patrickiel/pull-up-bar/cad/pull-up bar variants/biacromia breadth 37 cm (14.6 inch).pdf

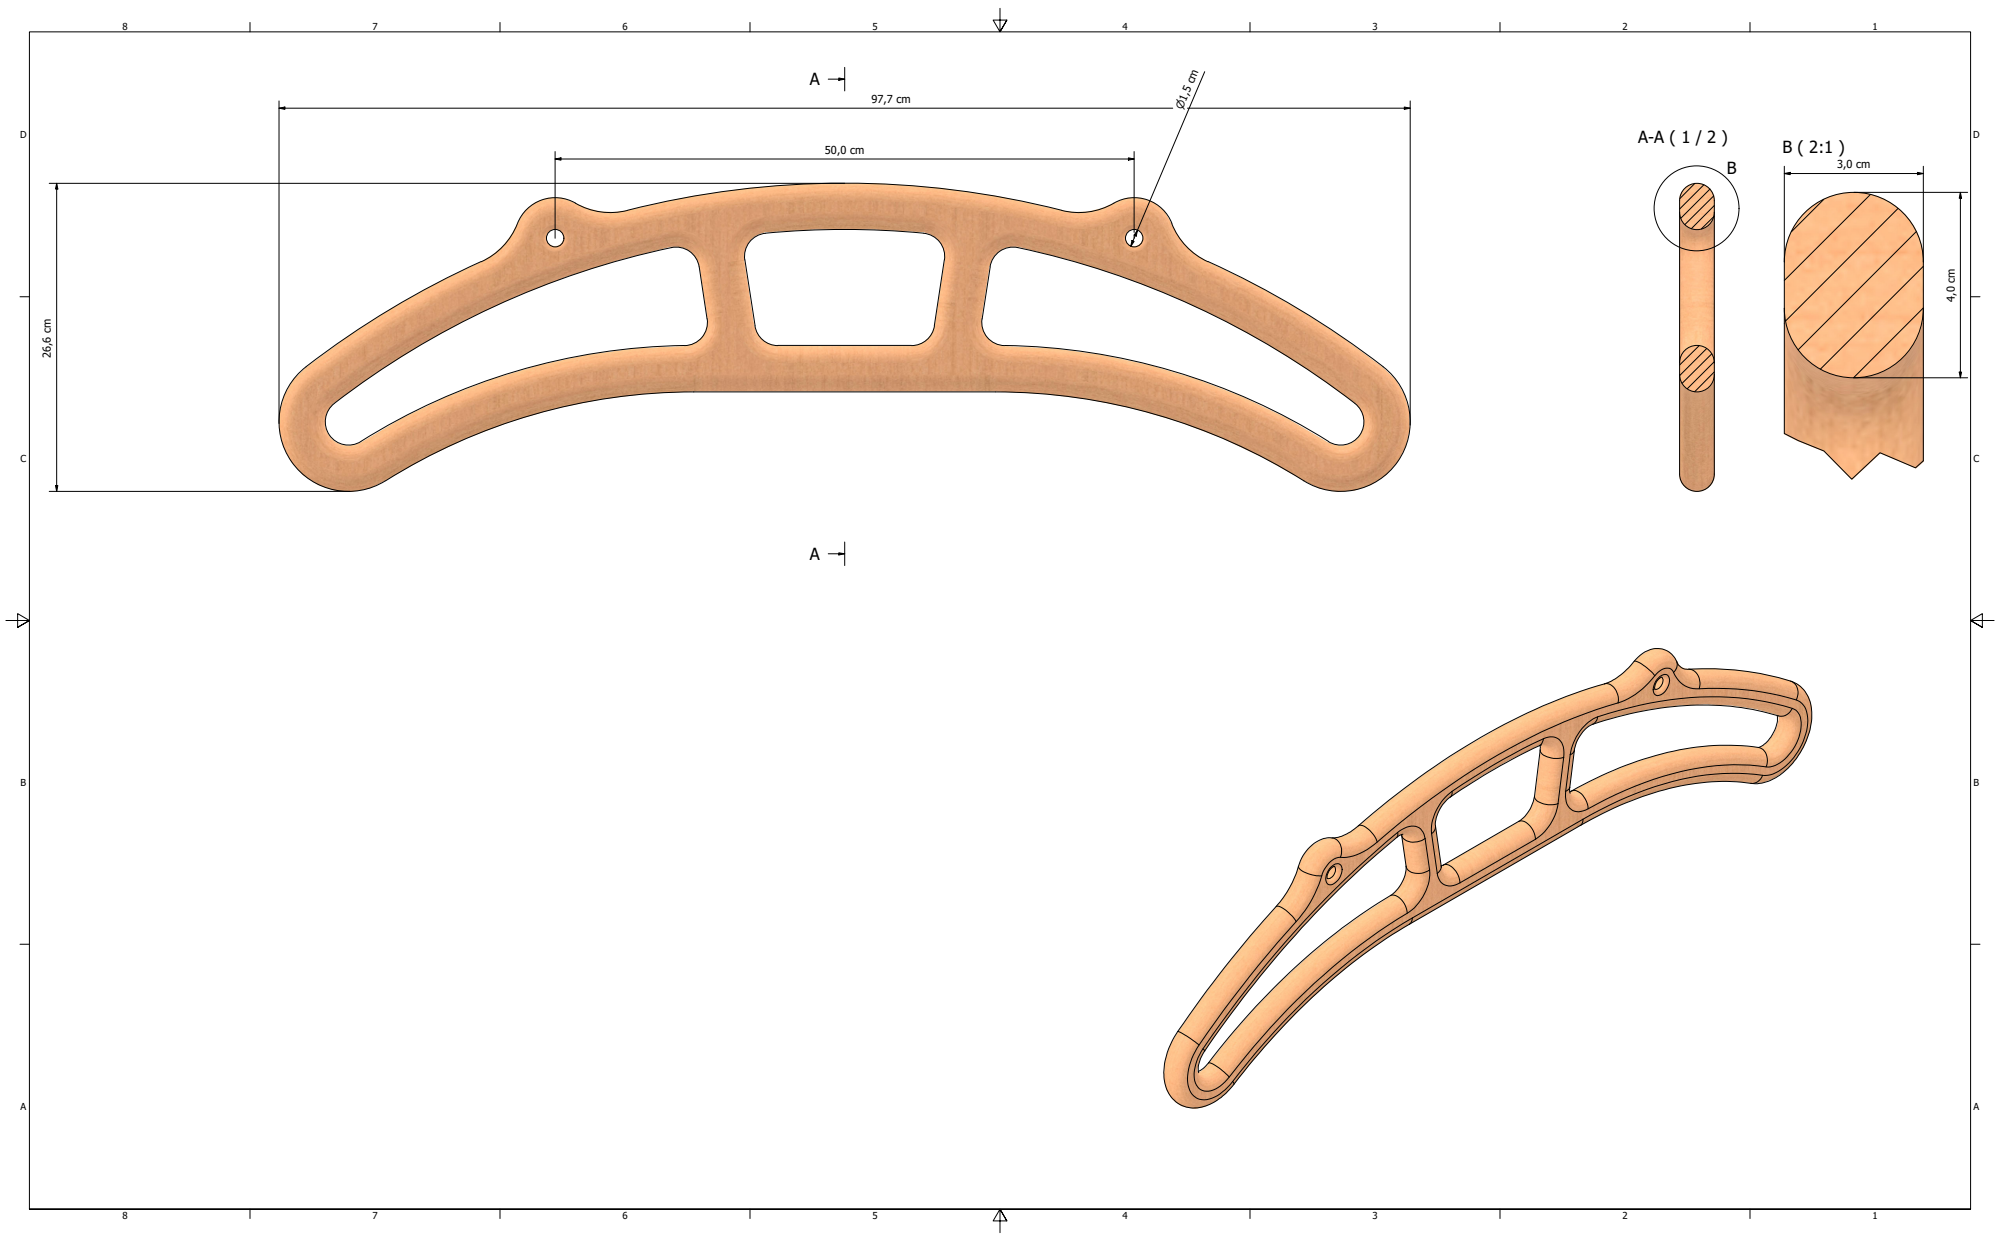
[picture p32: page 1]

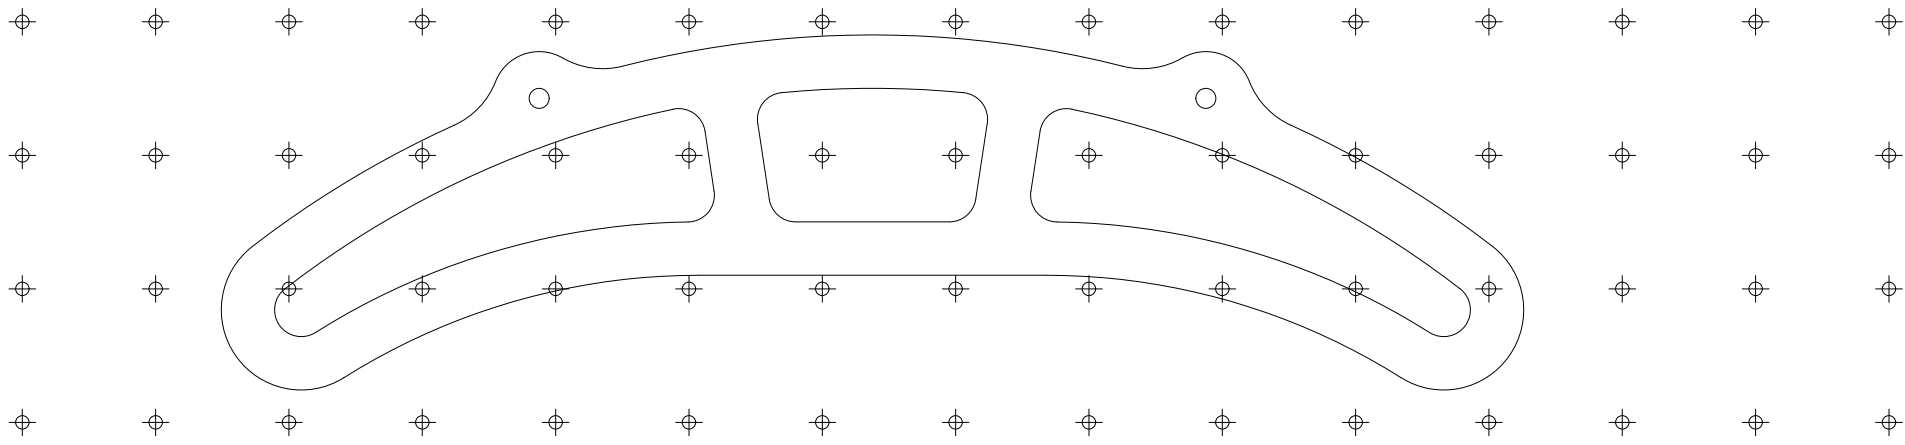
[picture p33: page 2]
