patrickiel/pull-up-bar/cad/pull-up bar variants/biacromia breadth 38 cm (15 inch).pdf

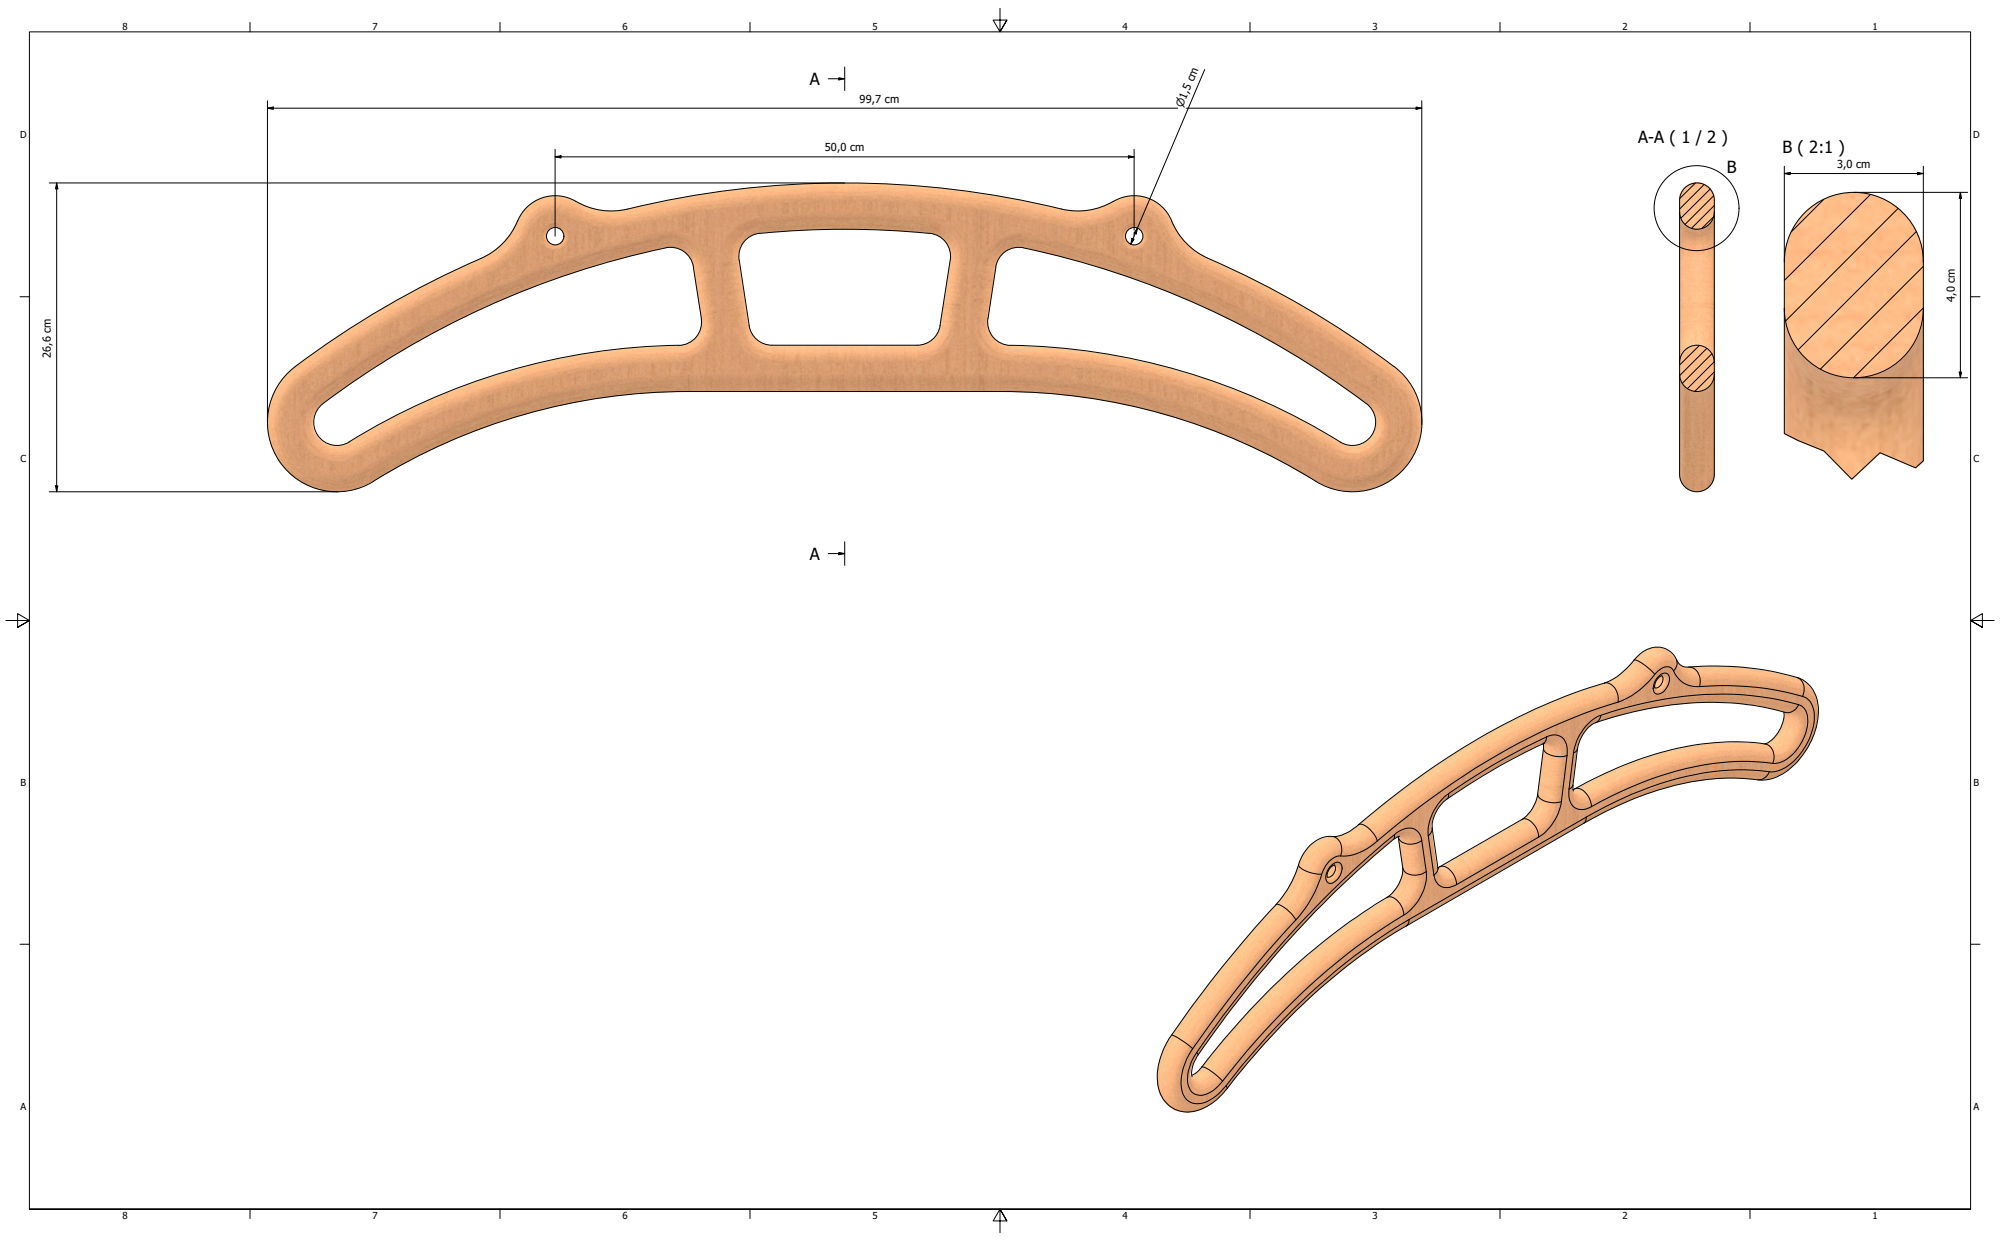
[picture p34: page 1]

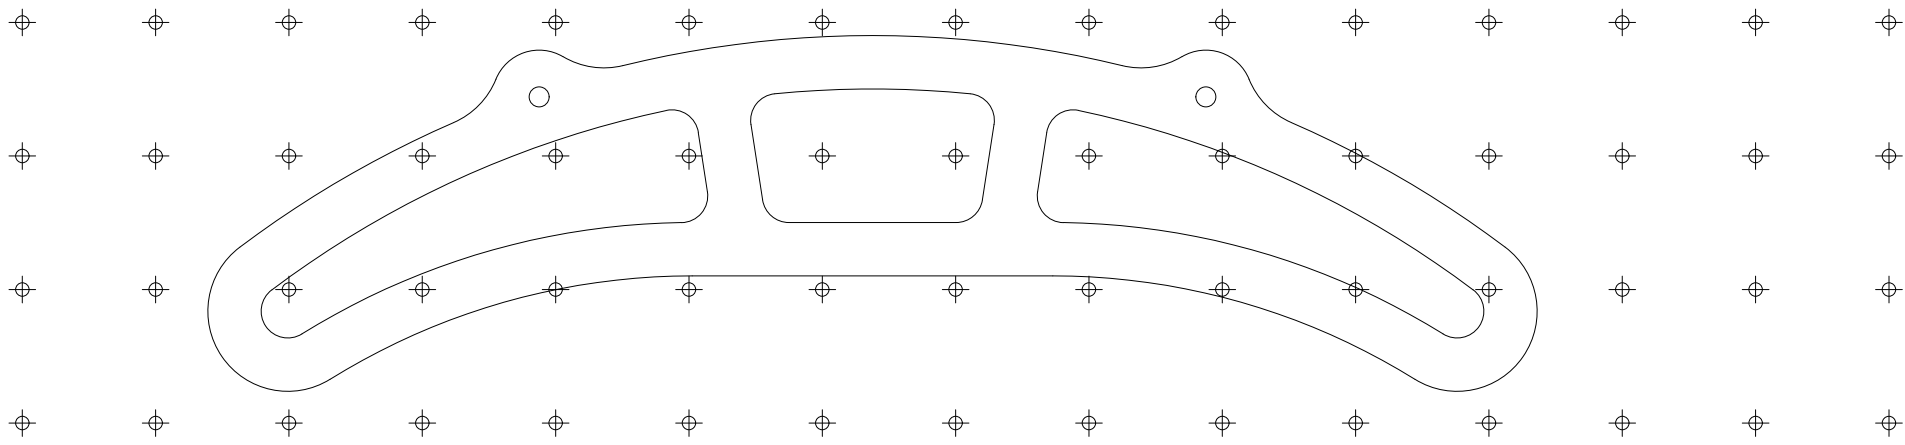
[picture p35: page 2]
