patrickiel/pull-up-bar/cad/pull-up bar variants/biacromia breadth 39 cm (15.4 inch).pdf

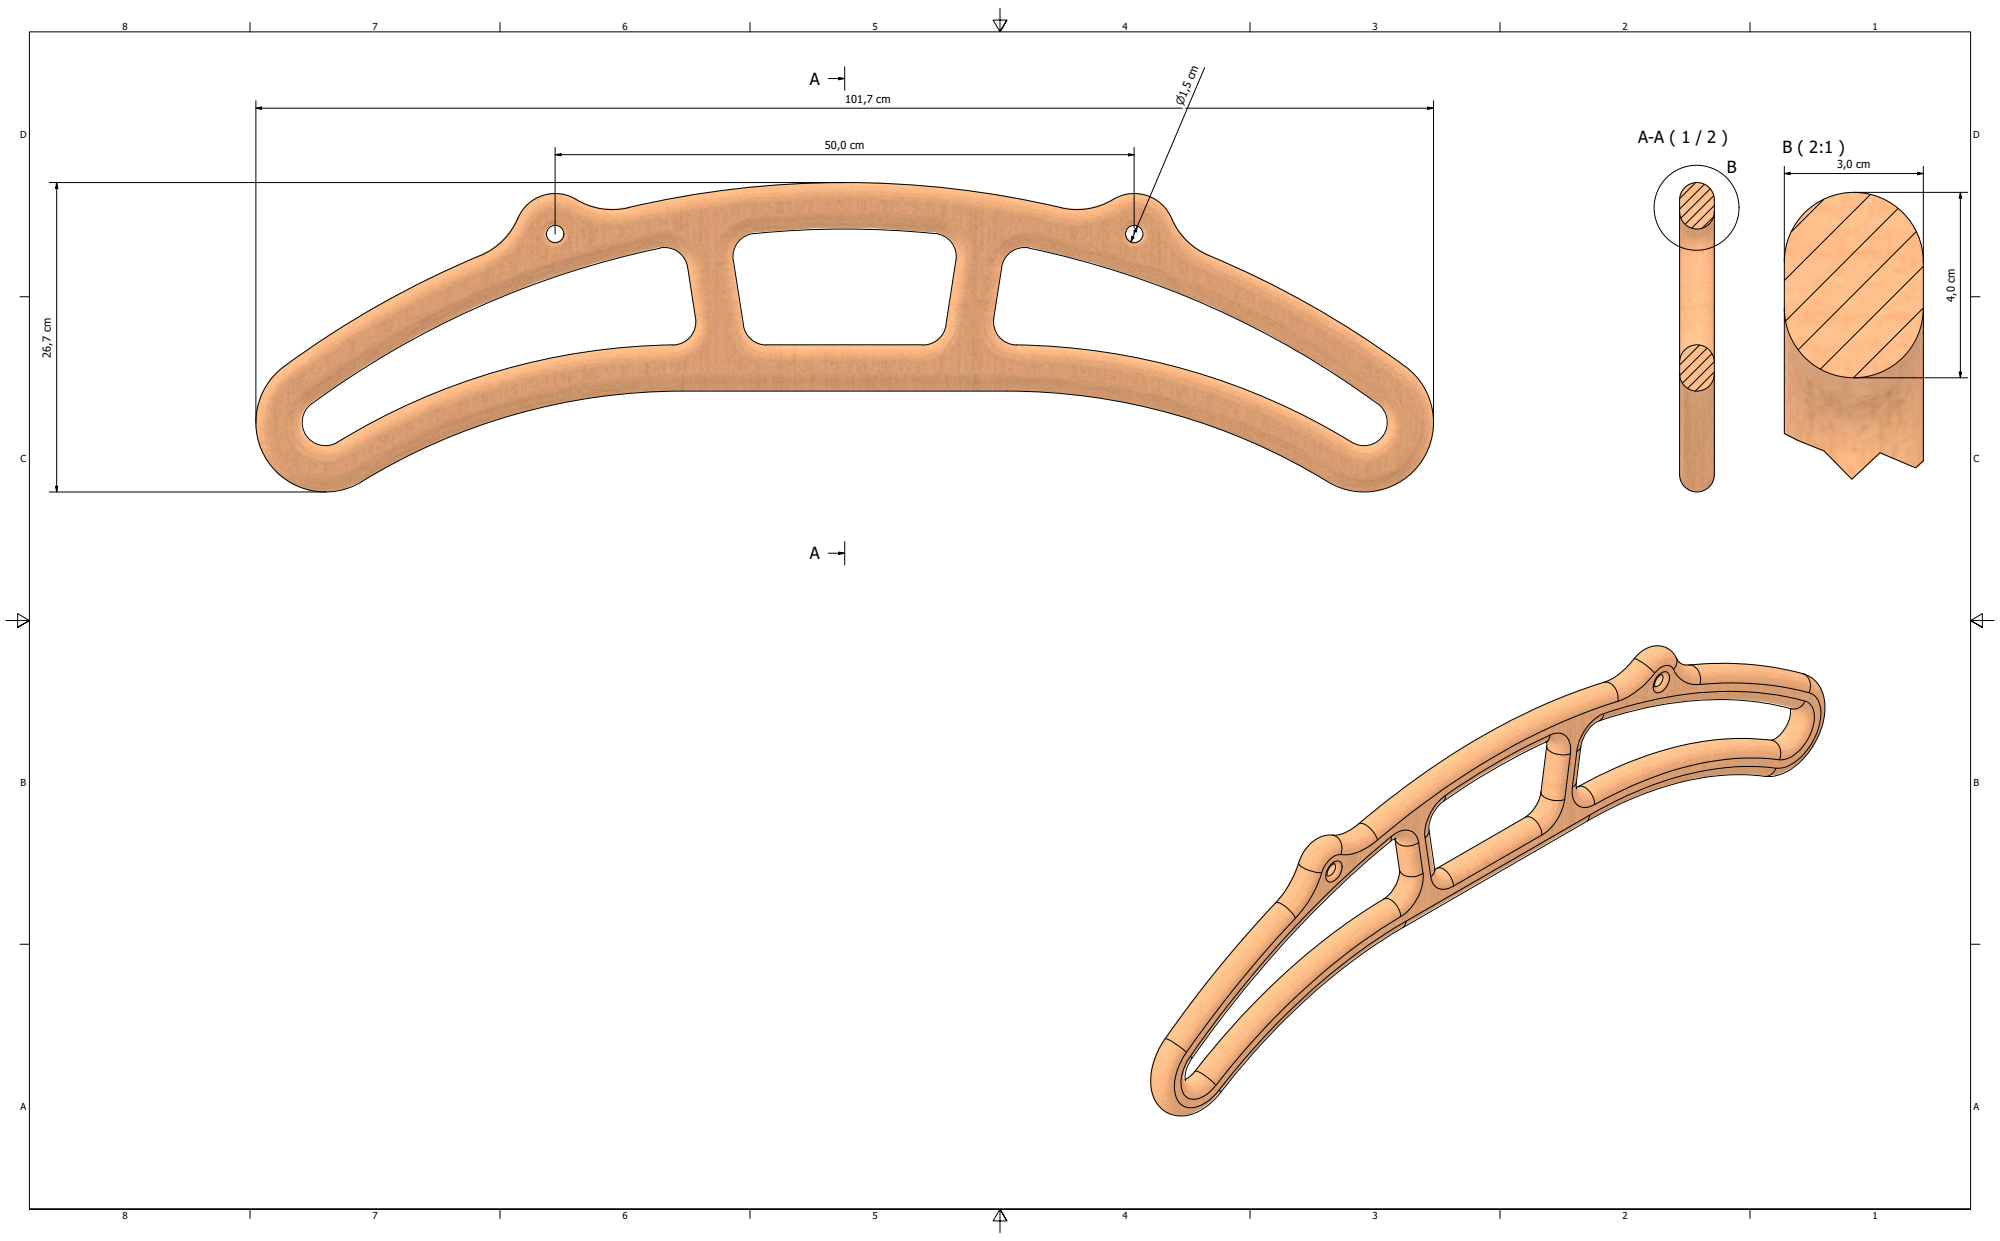
[picture p36: page 1]

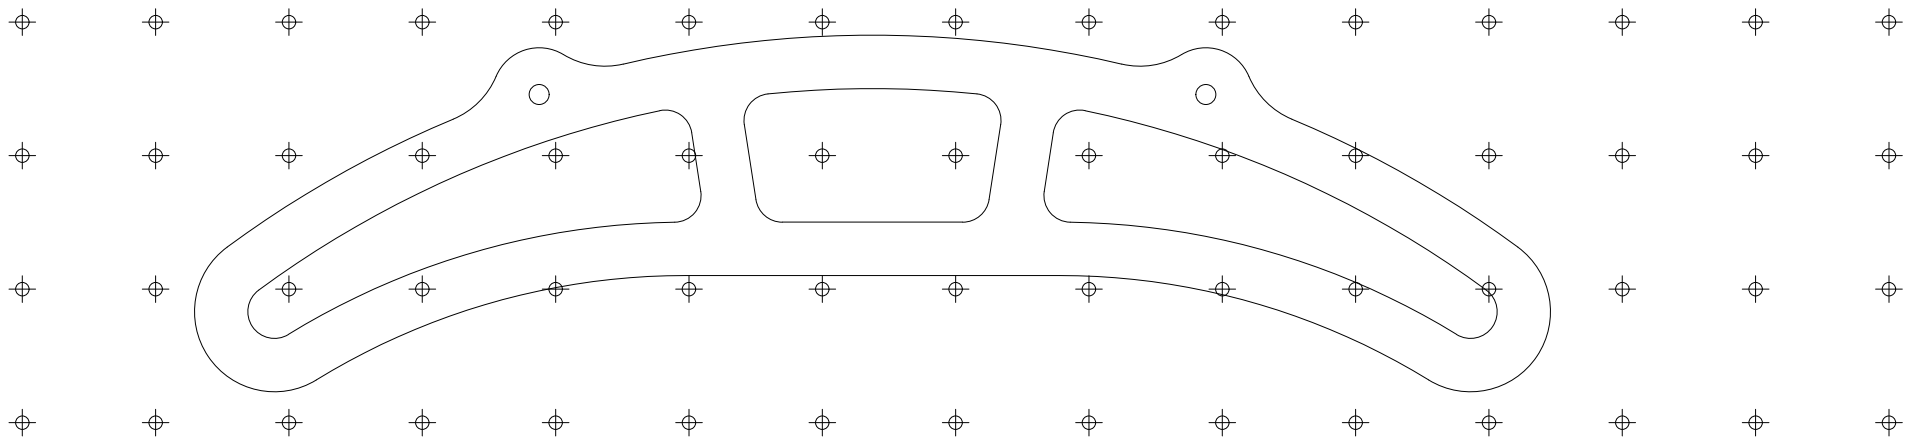
[picture p37: page 2]
