patrickiel/pull-up-bar/cad/pull-up bar variants/biacromia breadth 40 cm (15.7 inch).pdf

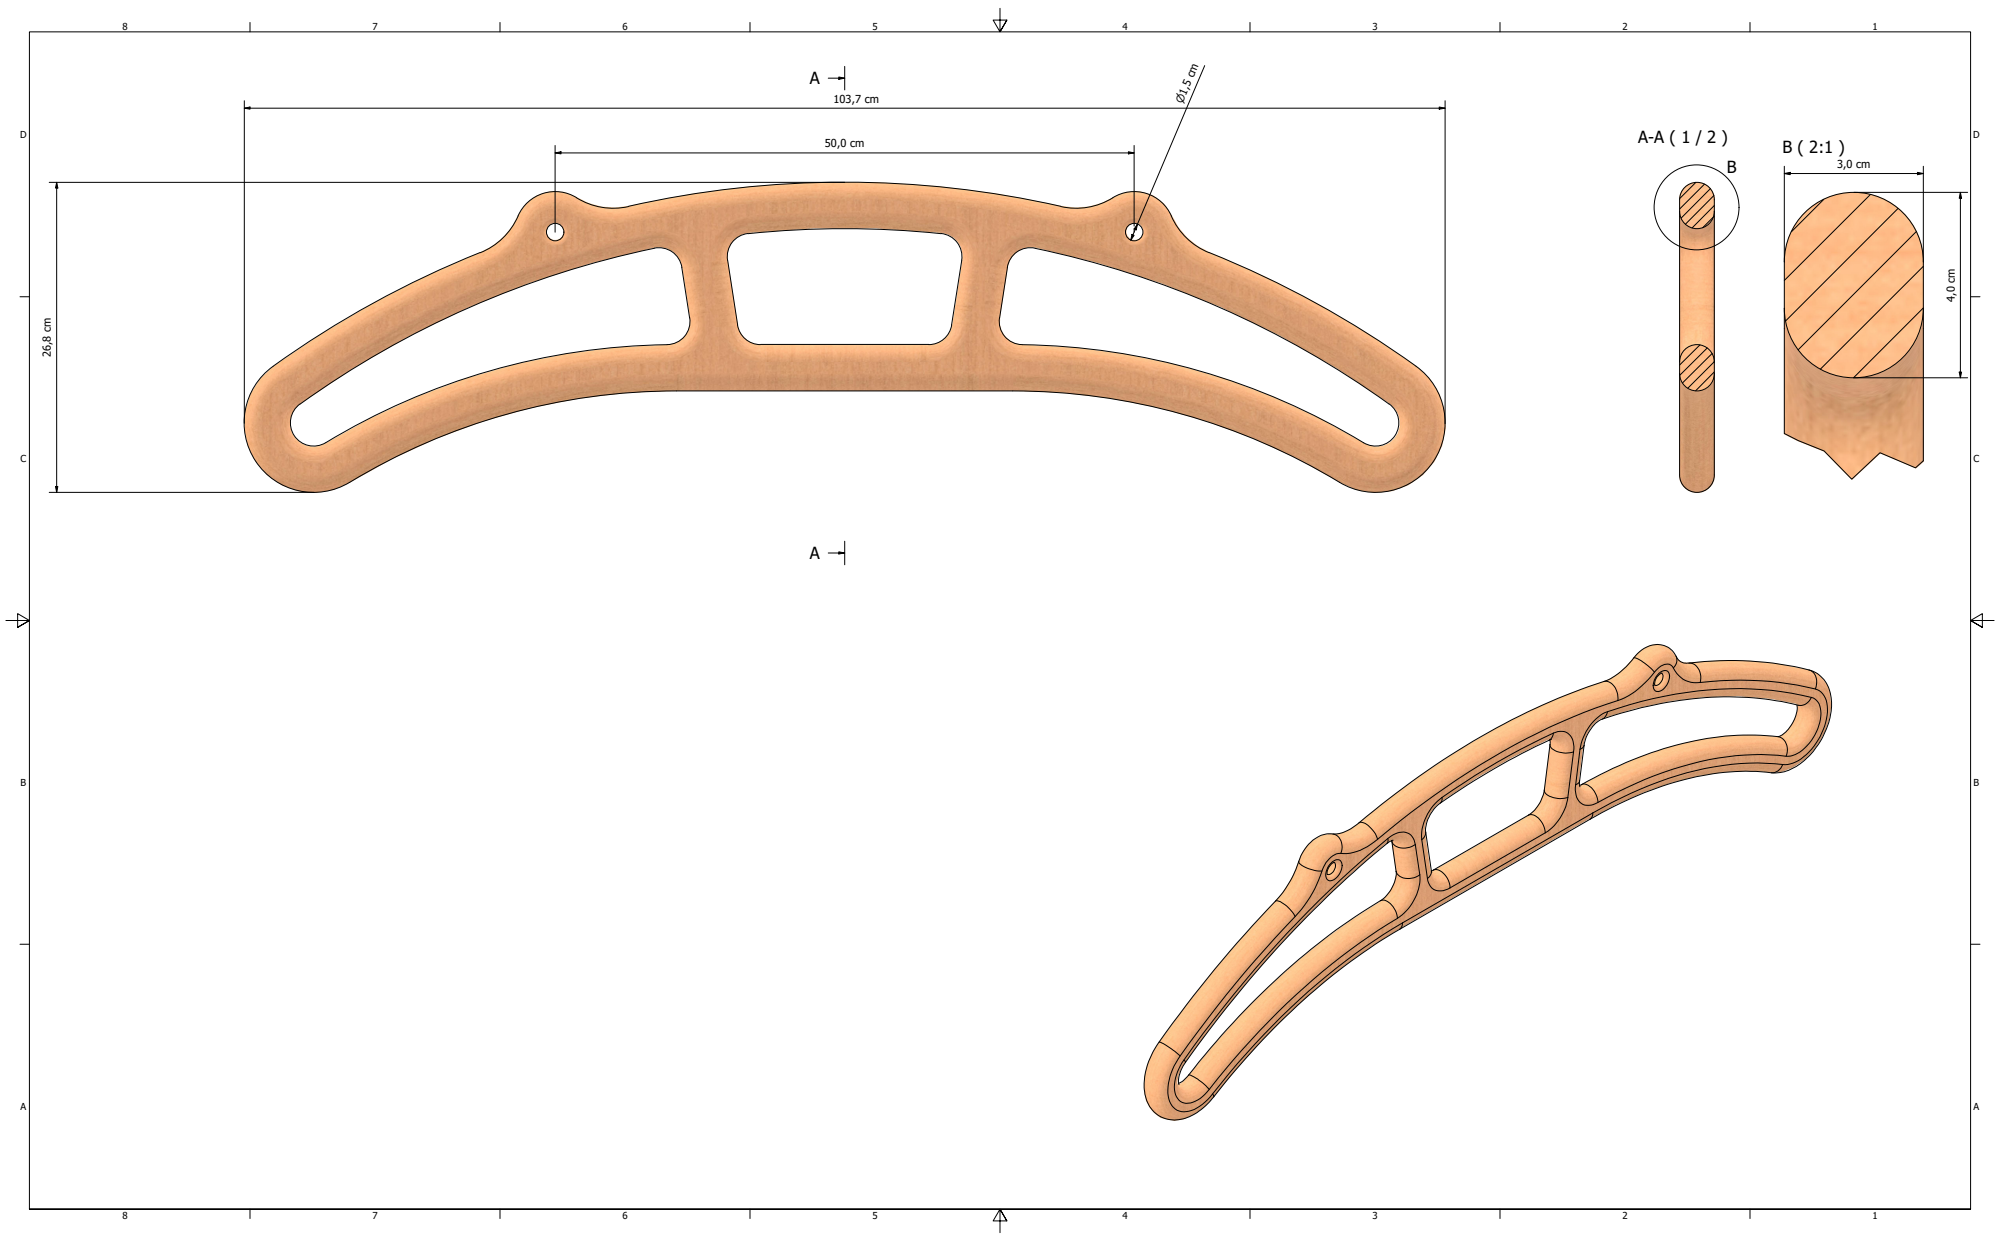
[picture p38: page 1]

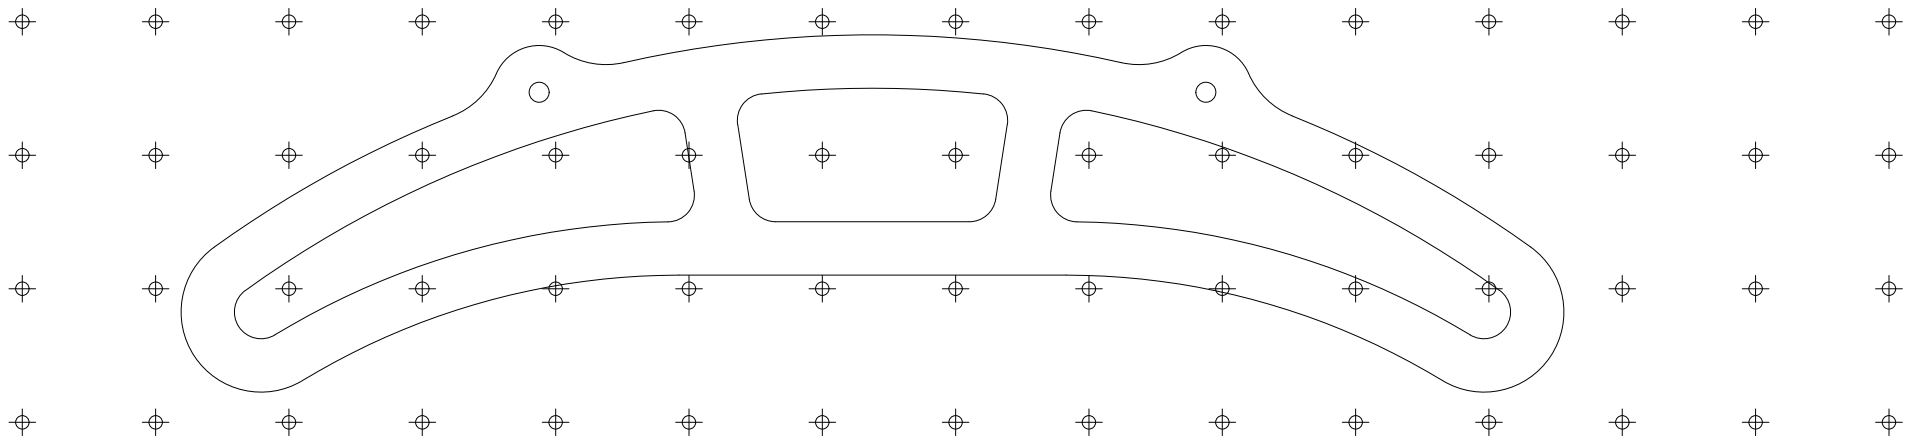
[picture p39: page 2]
