patrickiel/pull-up-bar/cad/pull-up bar variants/biacromia breadth 41 cm (16.1 inch).pdf

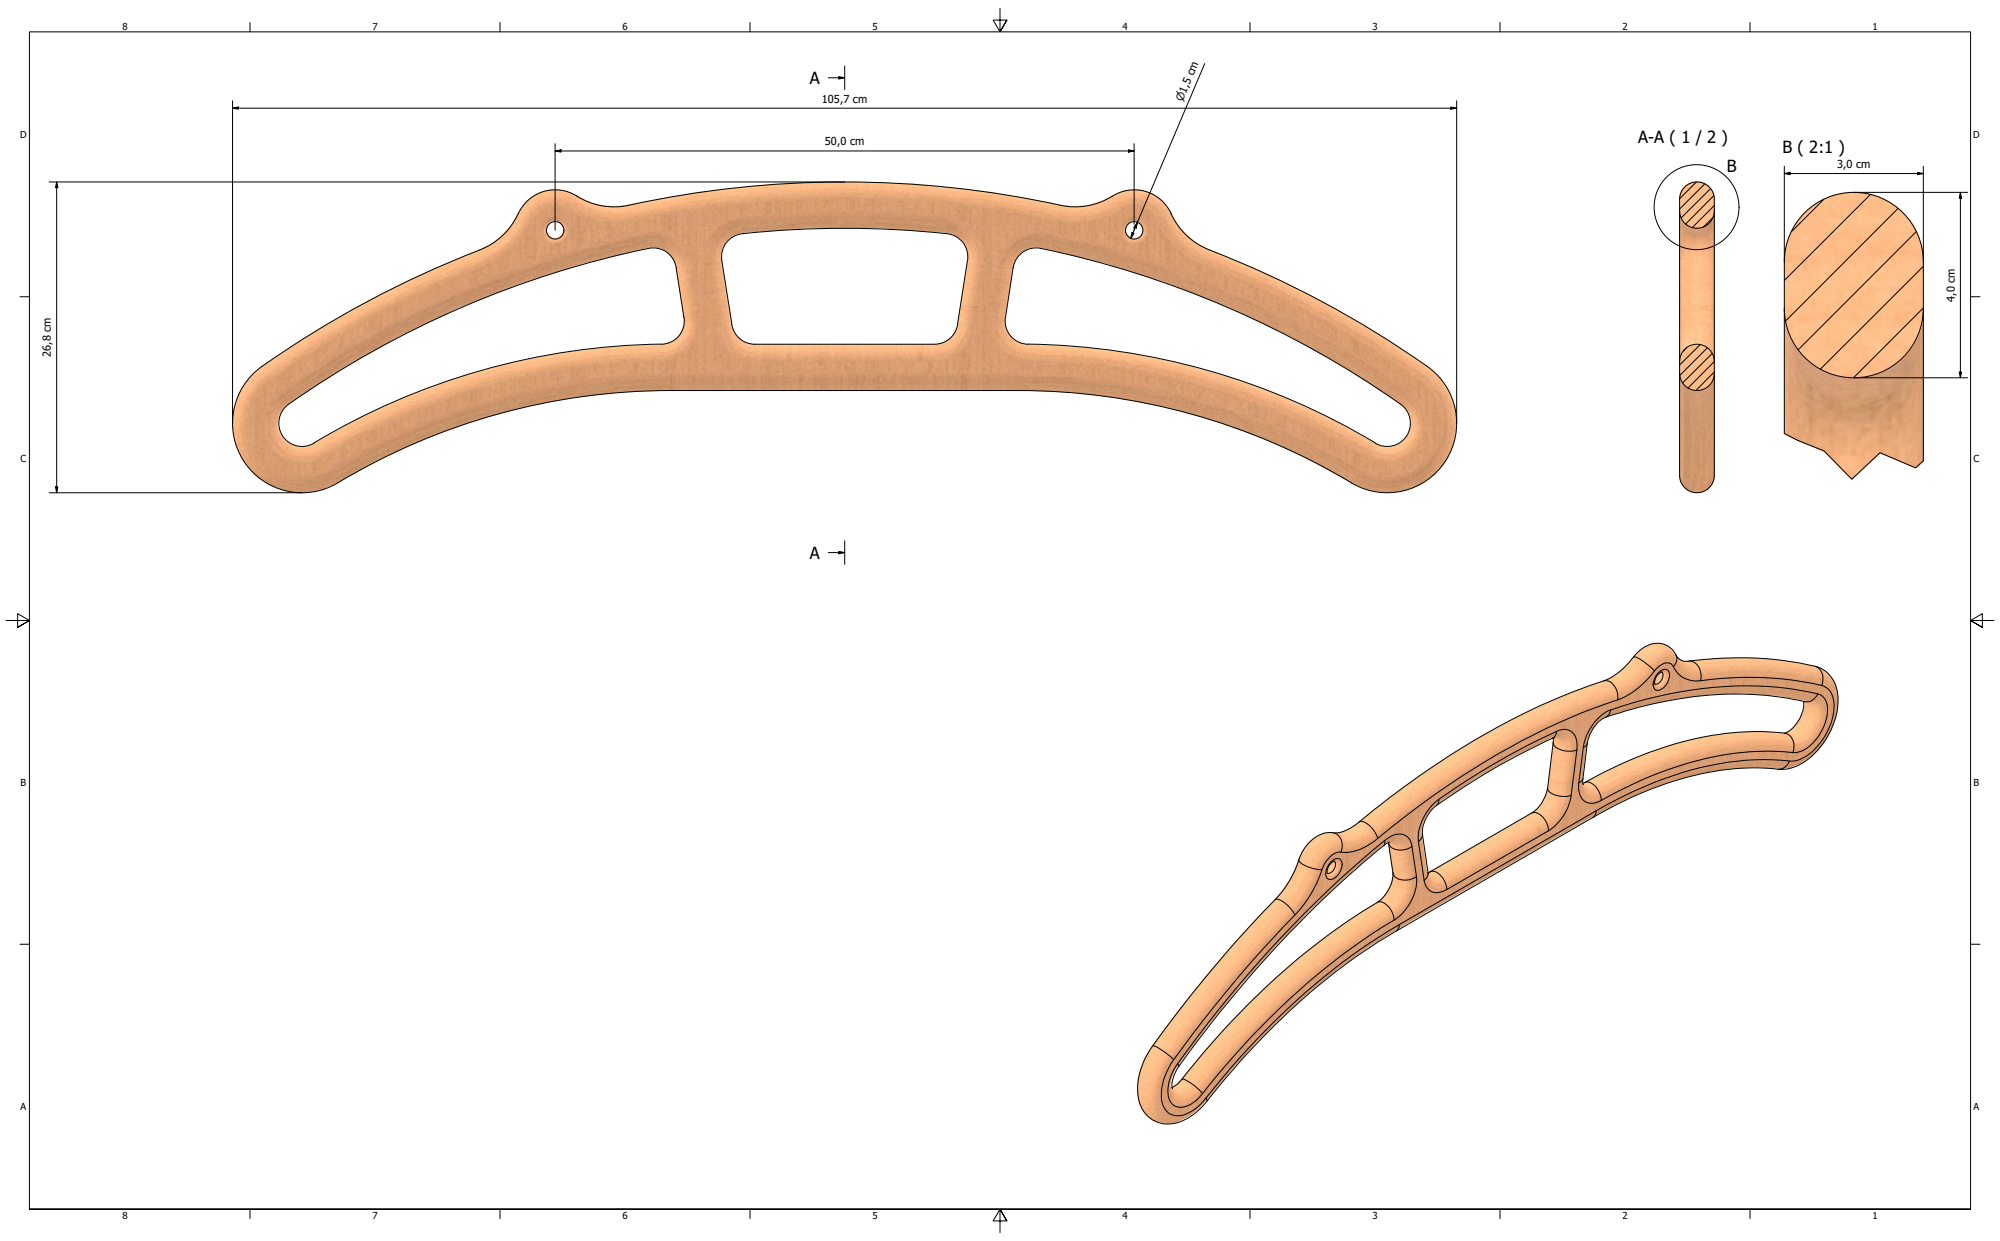
[picture p40: page 1]

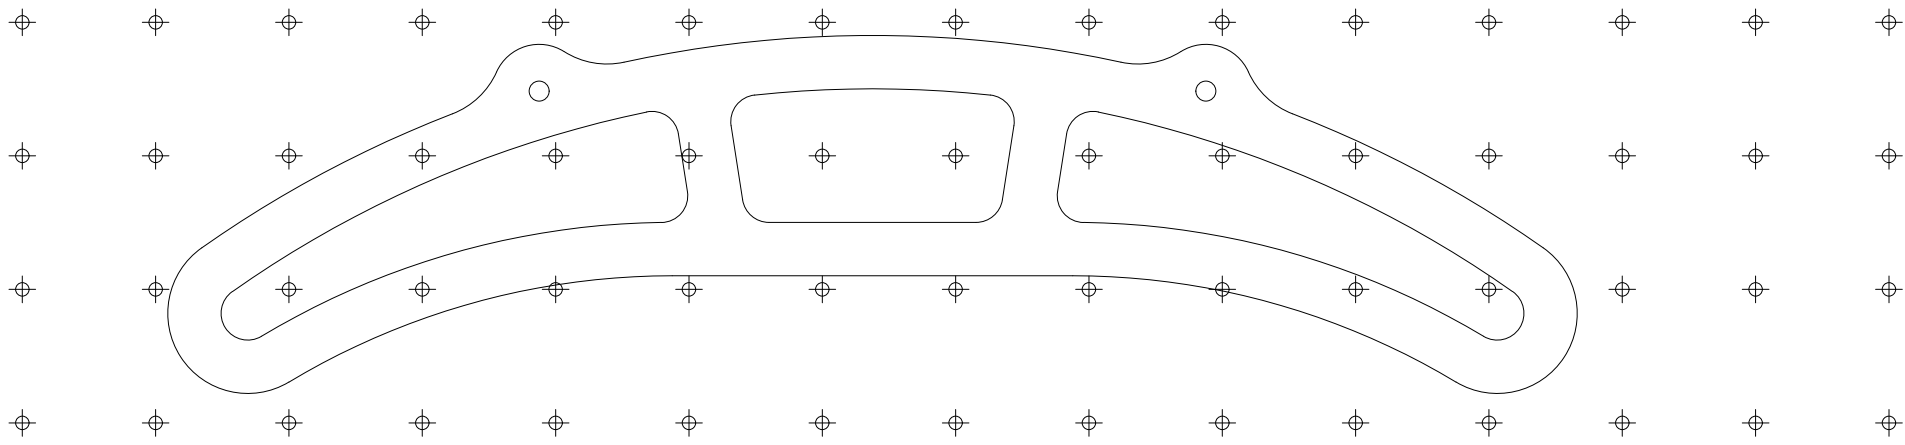
[picture p41: page 2]
