patrickiel/pull-up-bar/cad/pull-up bar variants/biacromia breadth 42 cm (16.5 inch).pdf

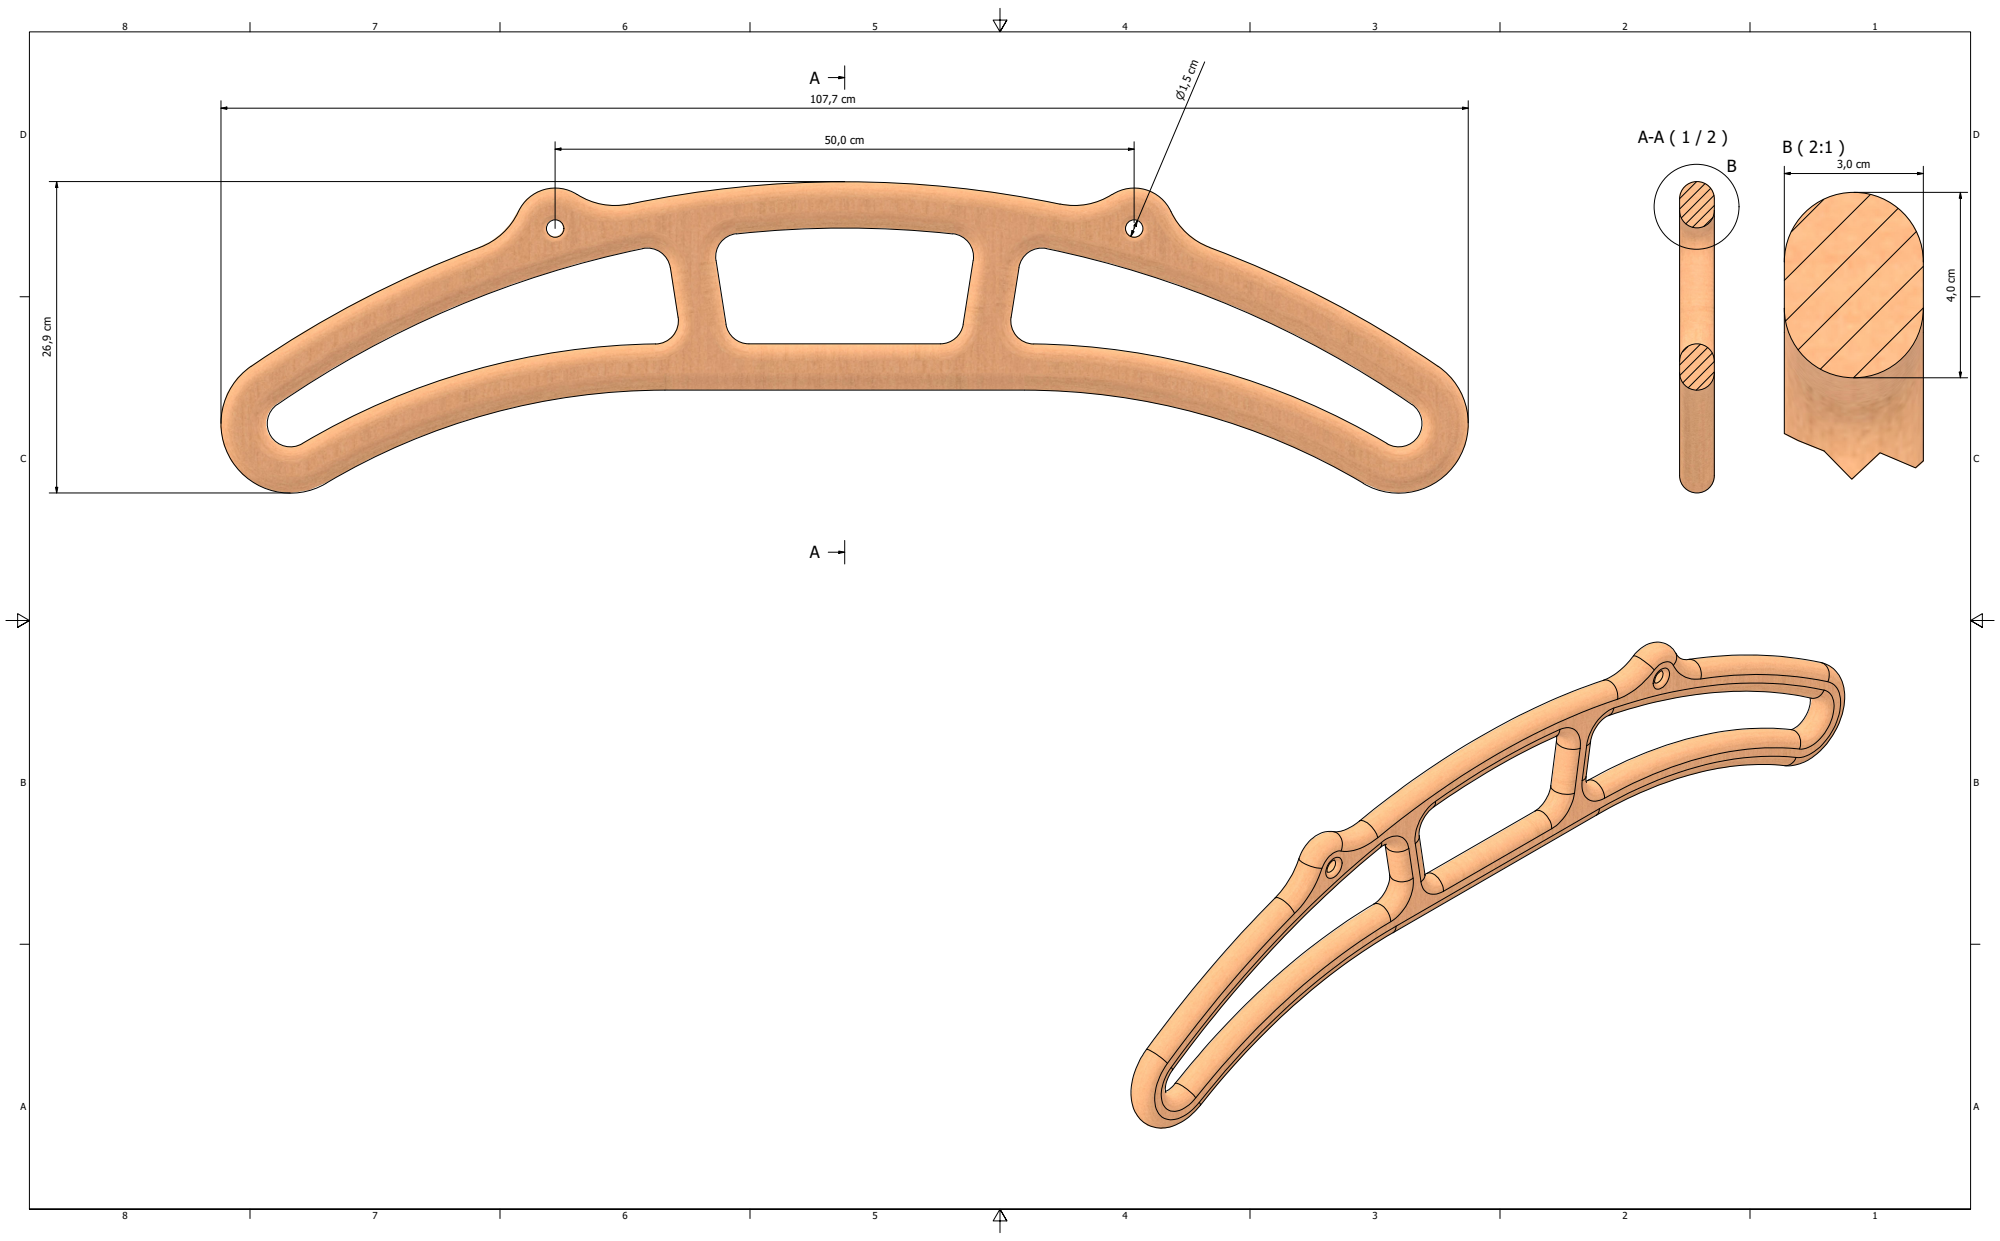
[picture p42: page 1]

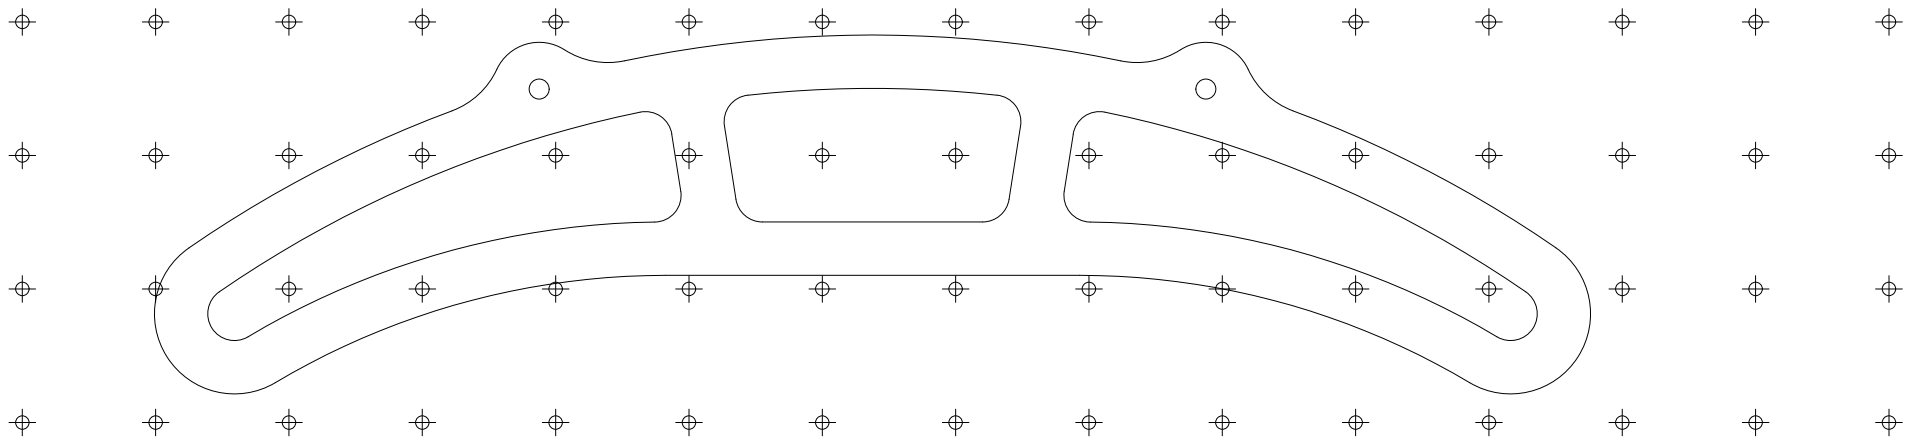
[picture p43: page 2]
