patrickiel/pull-up-bar/cad/pull-up bar variants/biacromia breadth 43 cm (16.9 inch).pdf

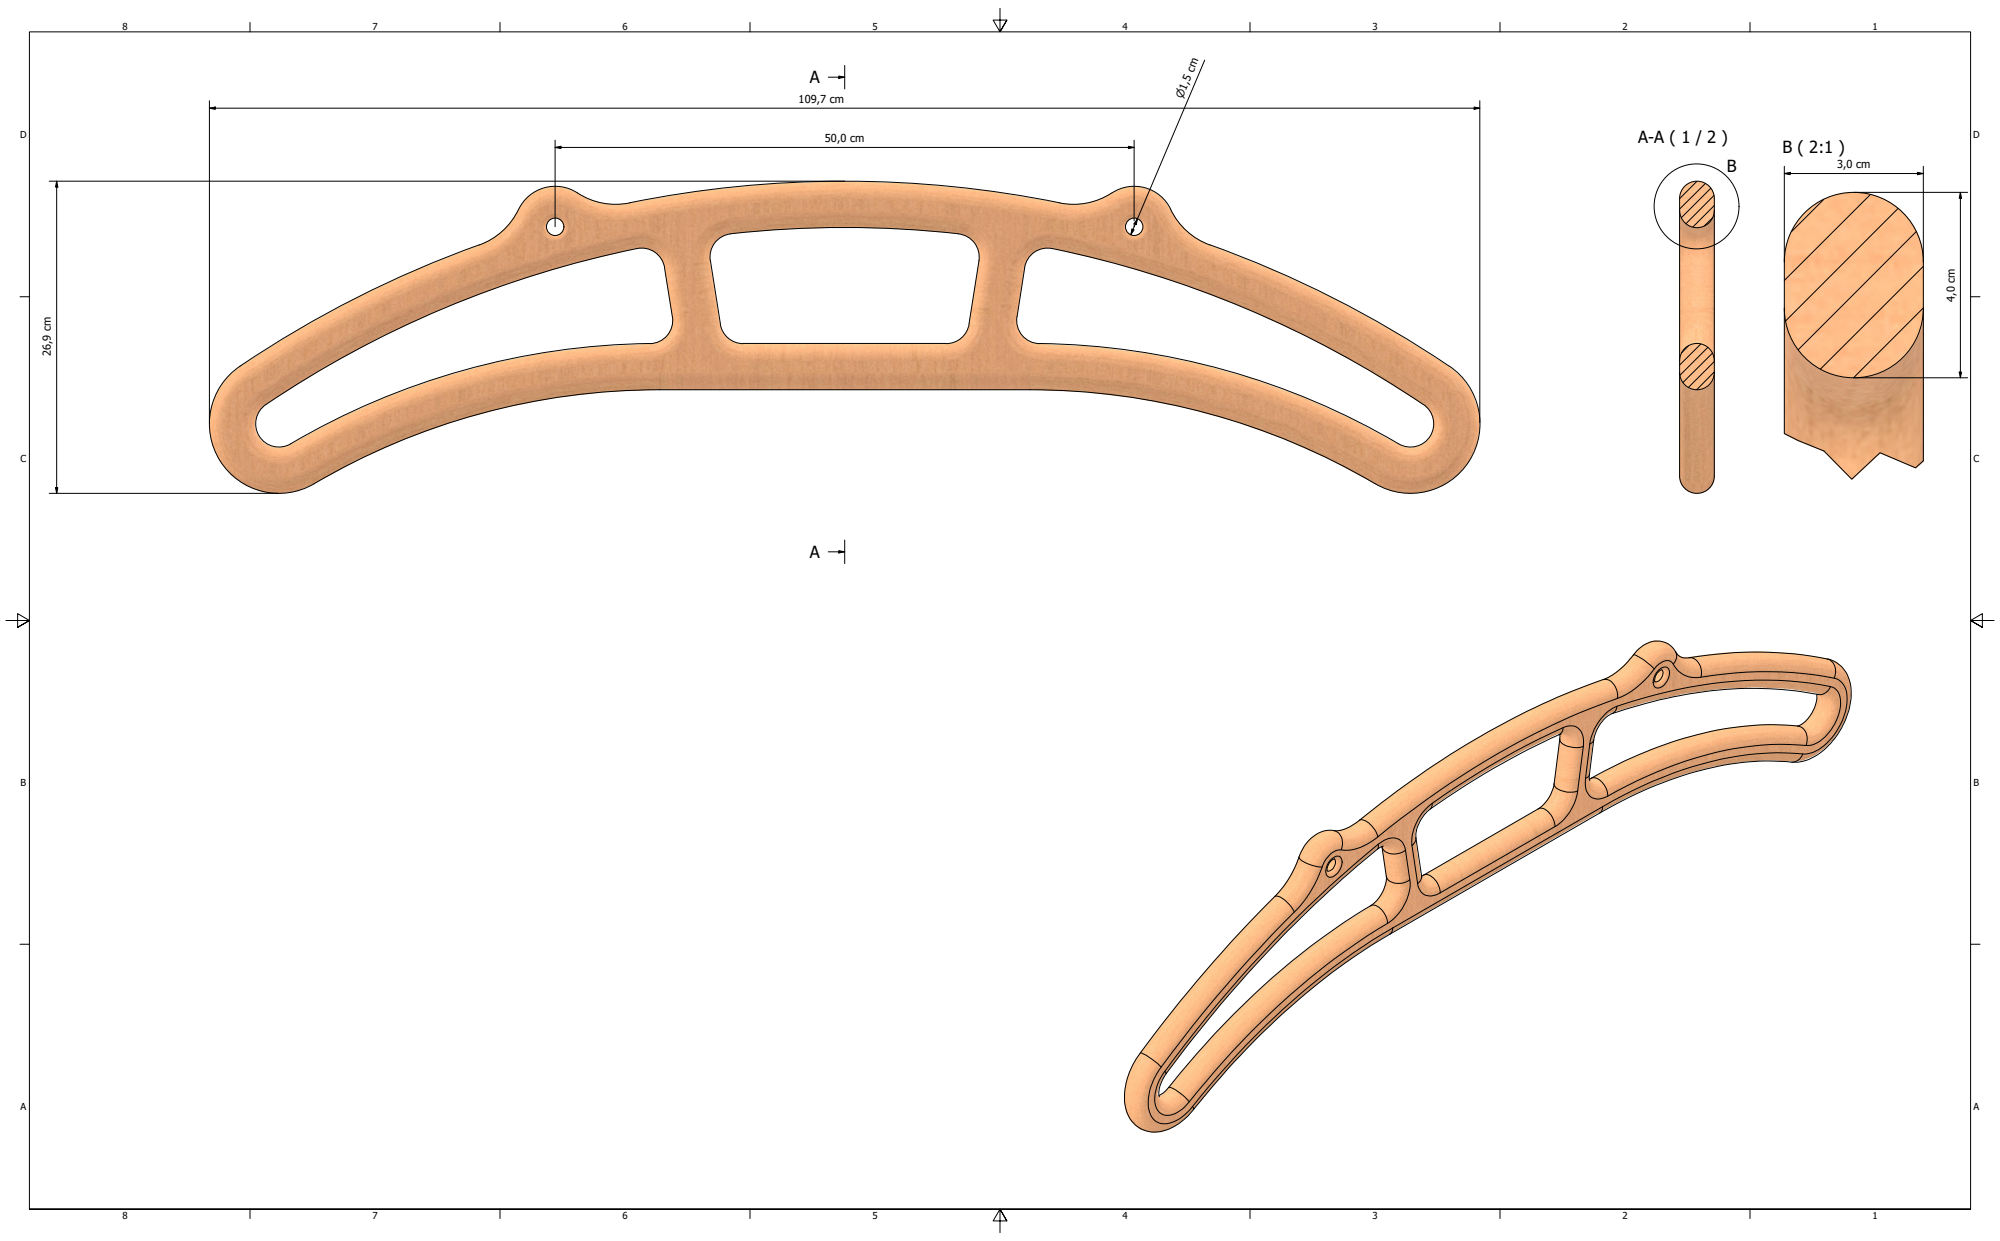
[picture p44: page 1]

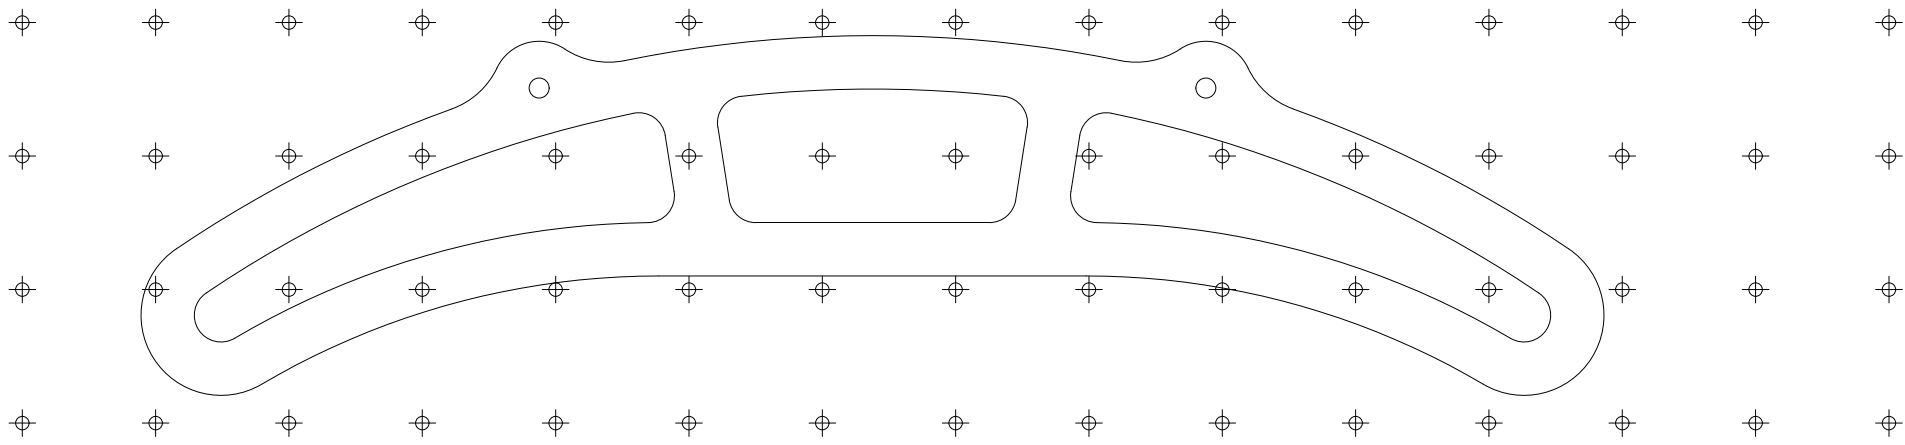
[picture p45: page 2]
