patrickiel/pull-up-bar/cad/pull-up bar variants/biacromia breadth 44 cm (17.3 inch).pdf

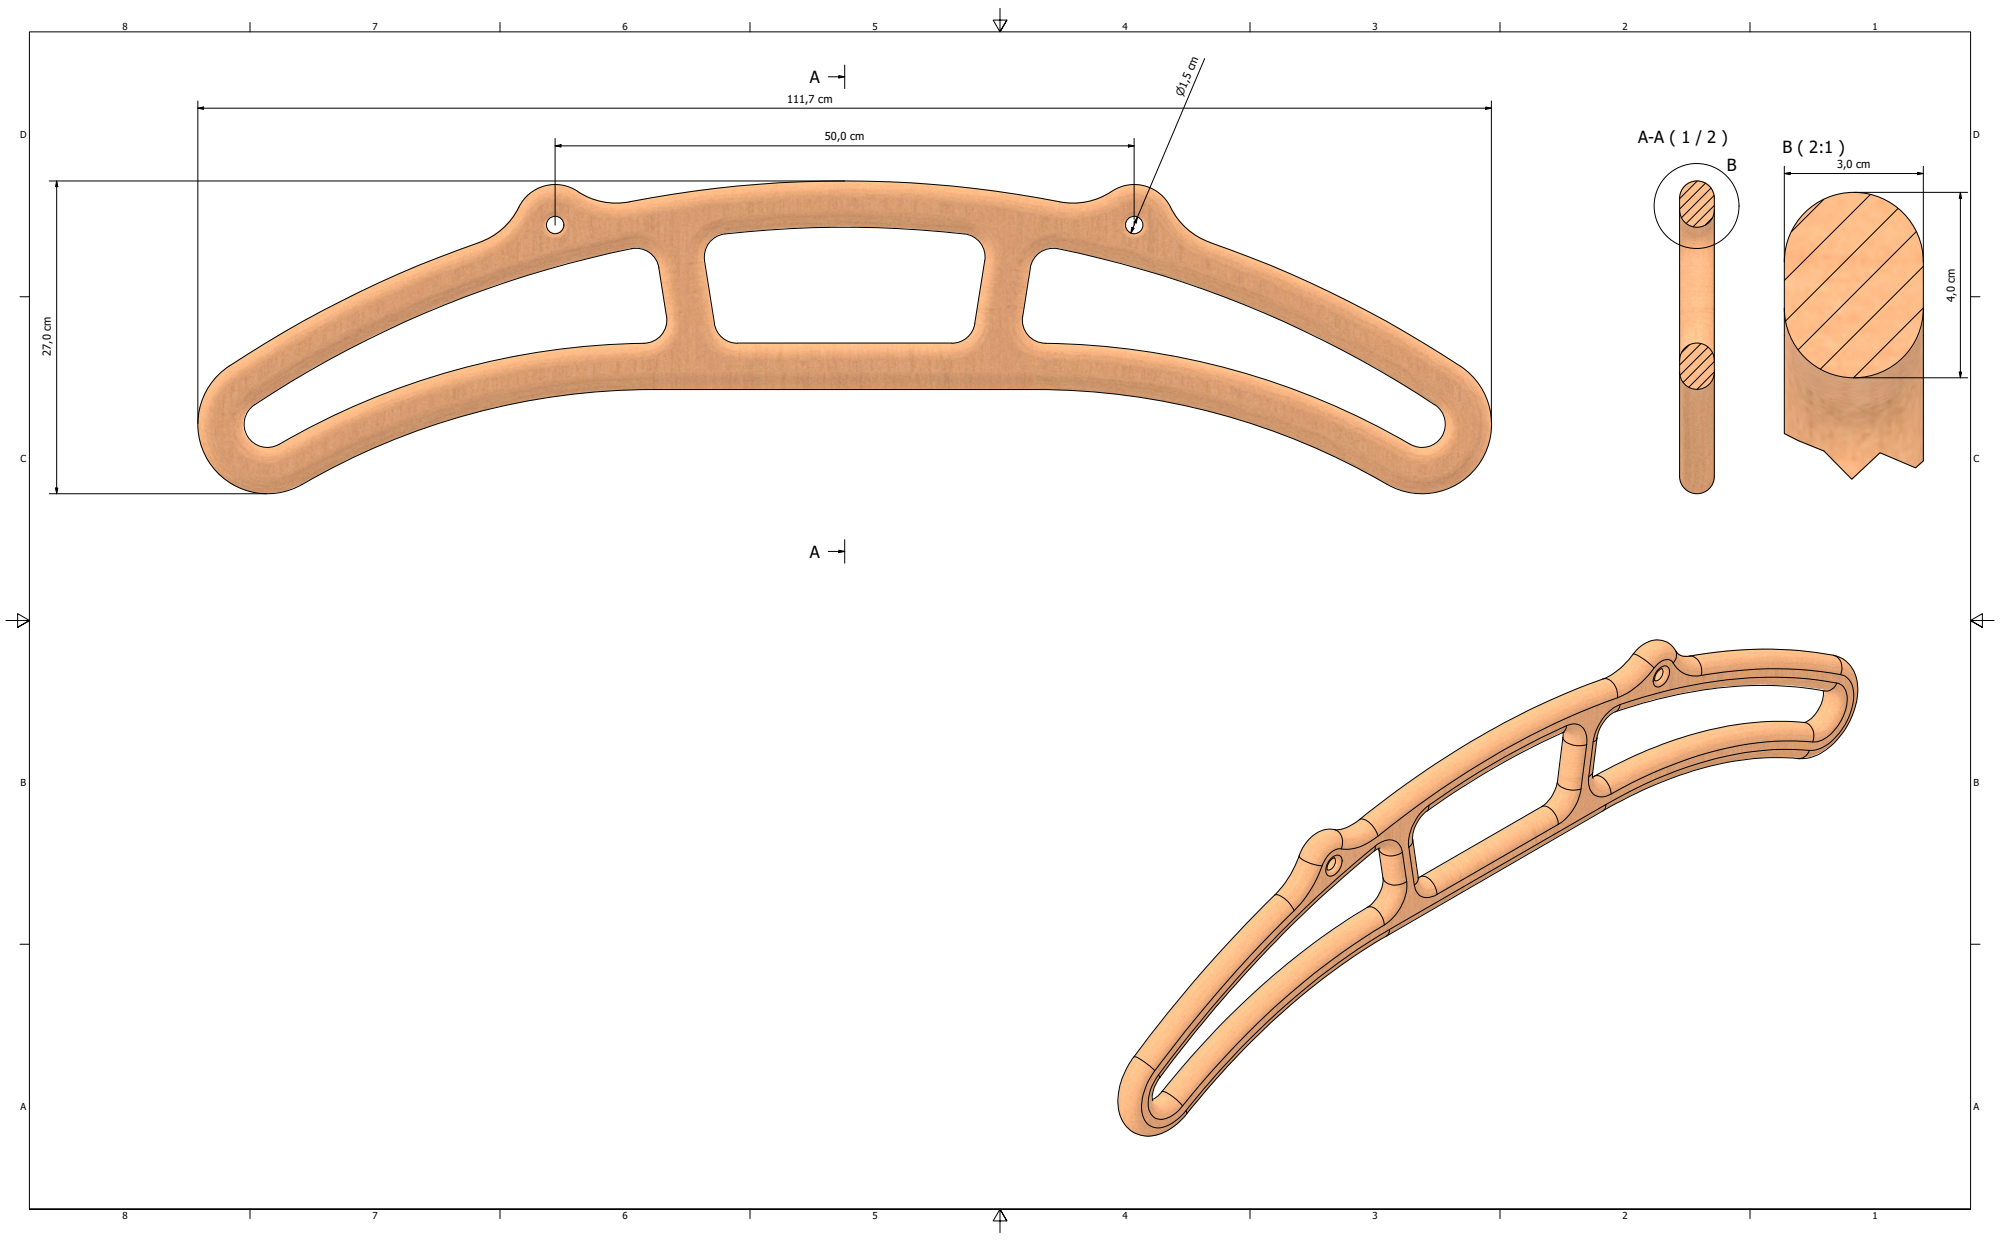
[picture p46: page 1]

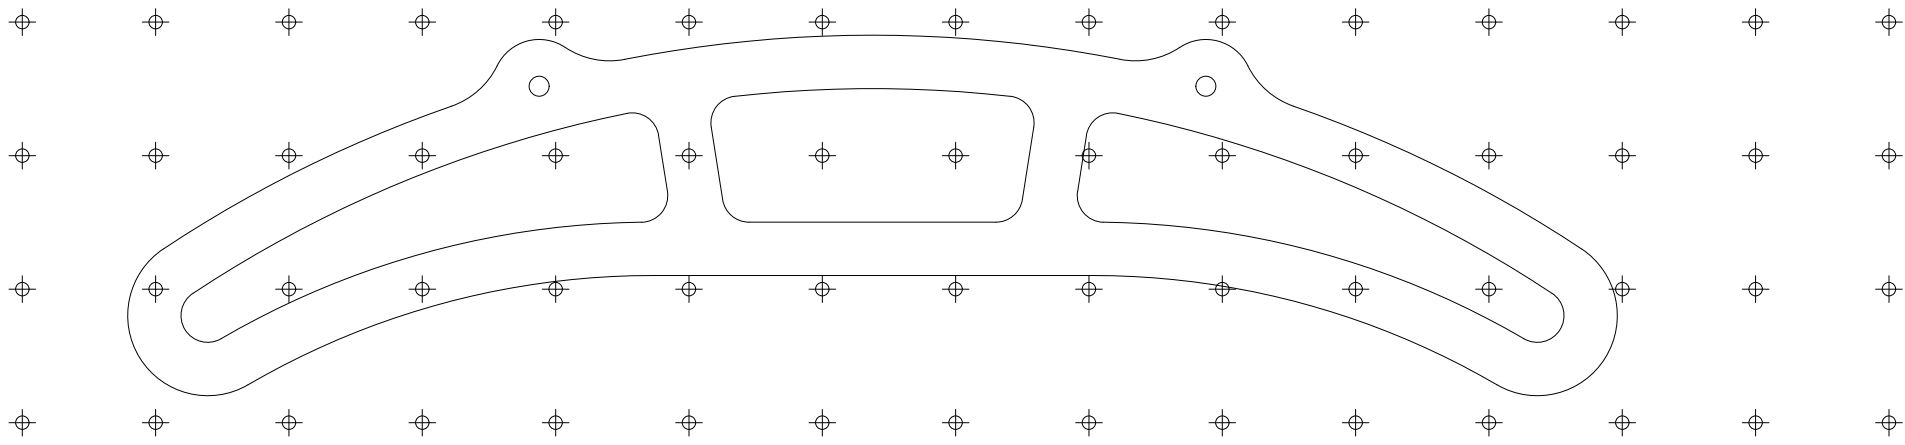
[picture p47: page 2]
