patrickiel/pull-up-bar/cad/pull-up bar variants/biacromia breadth 45 cm (17.7 inch).pdf

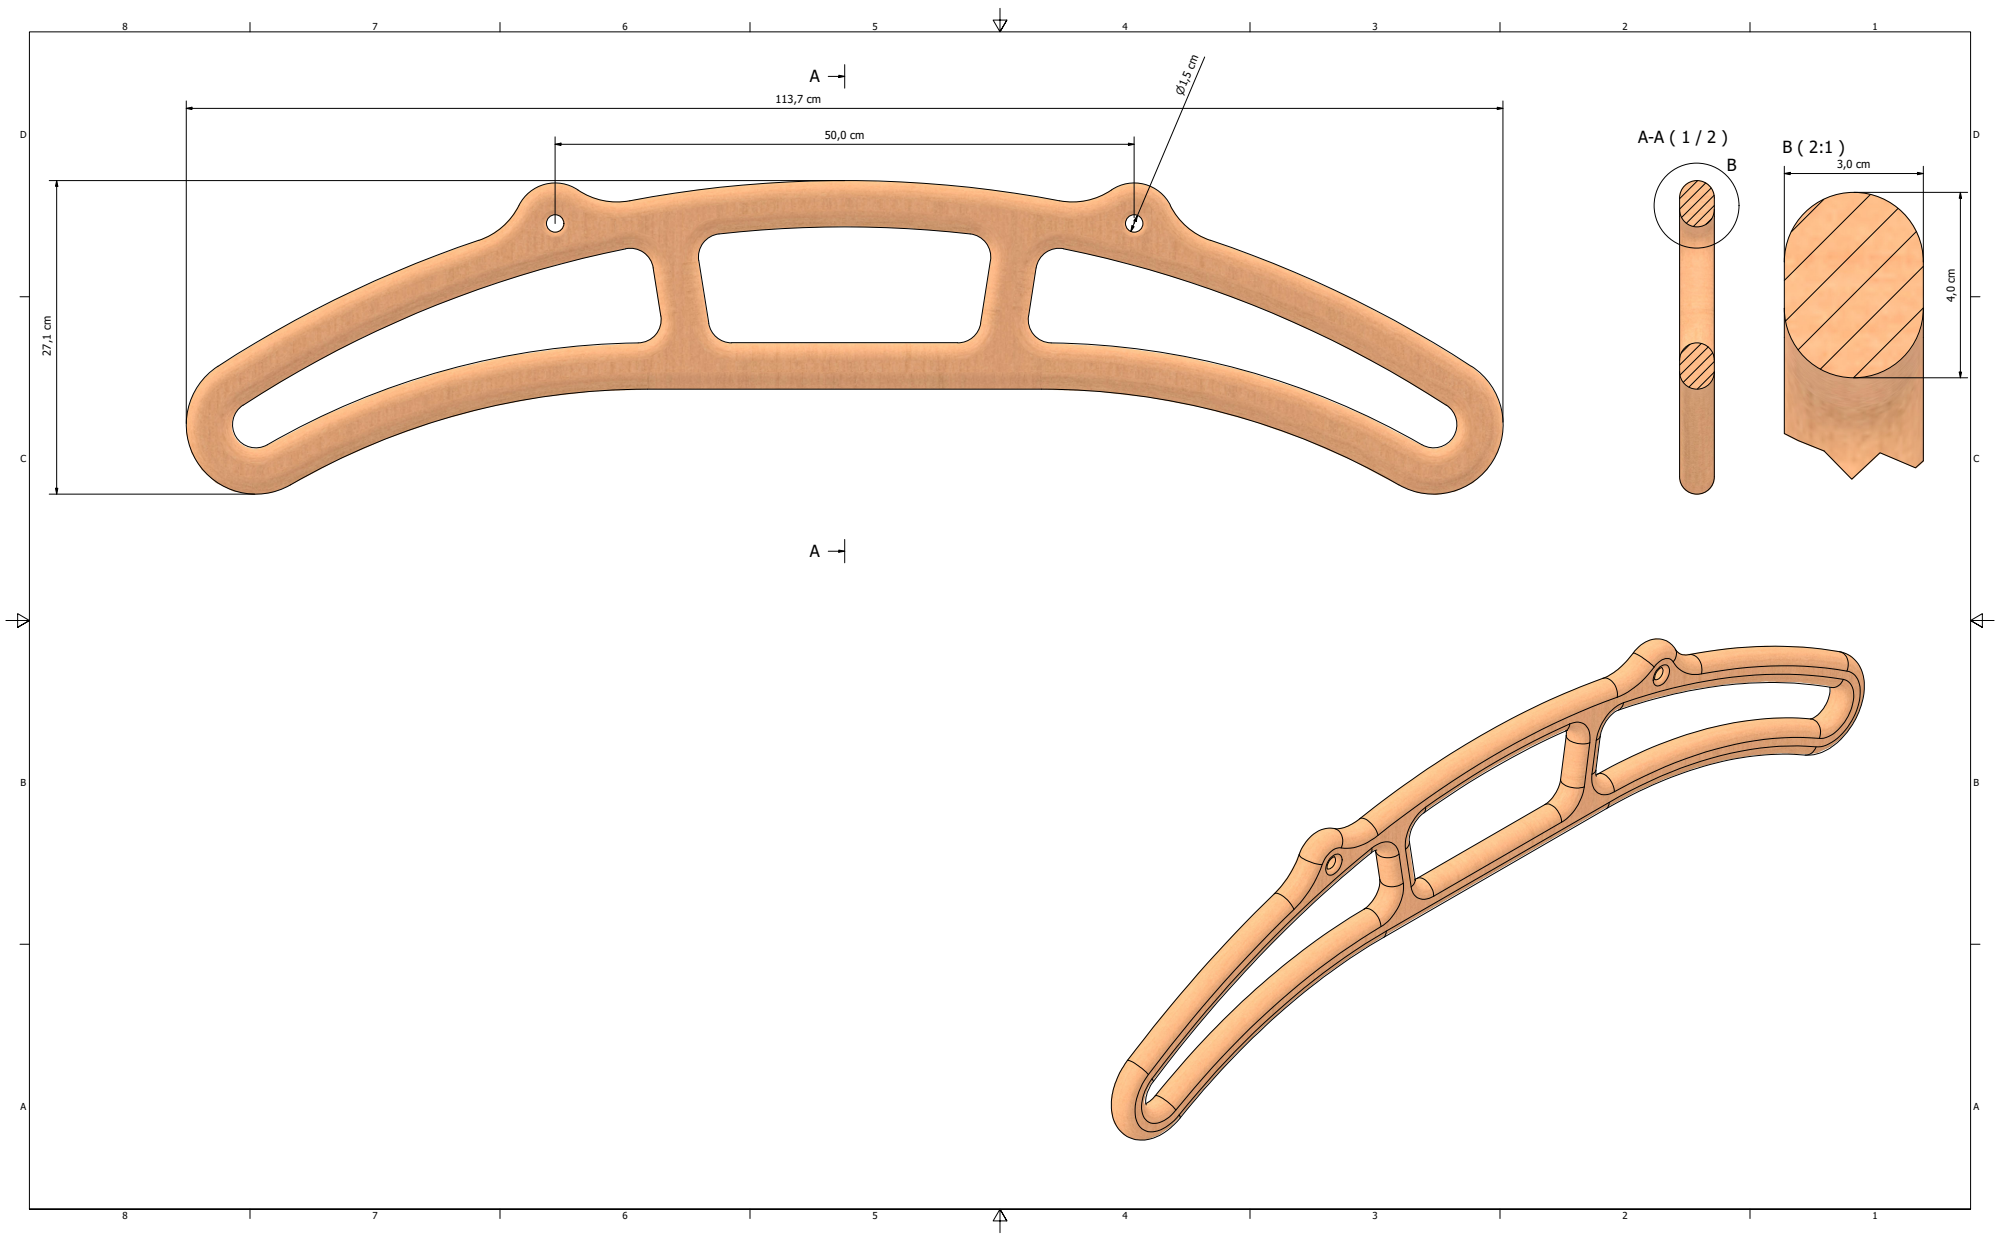
[picture p48: page 1]

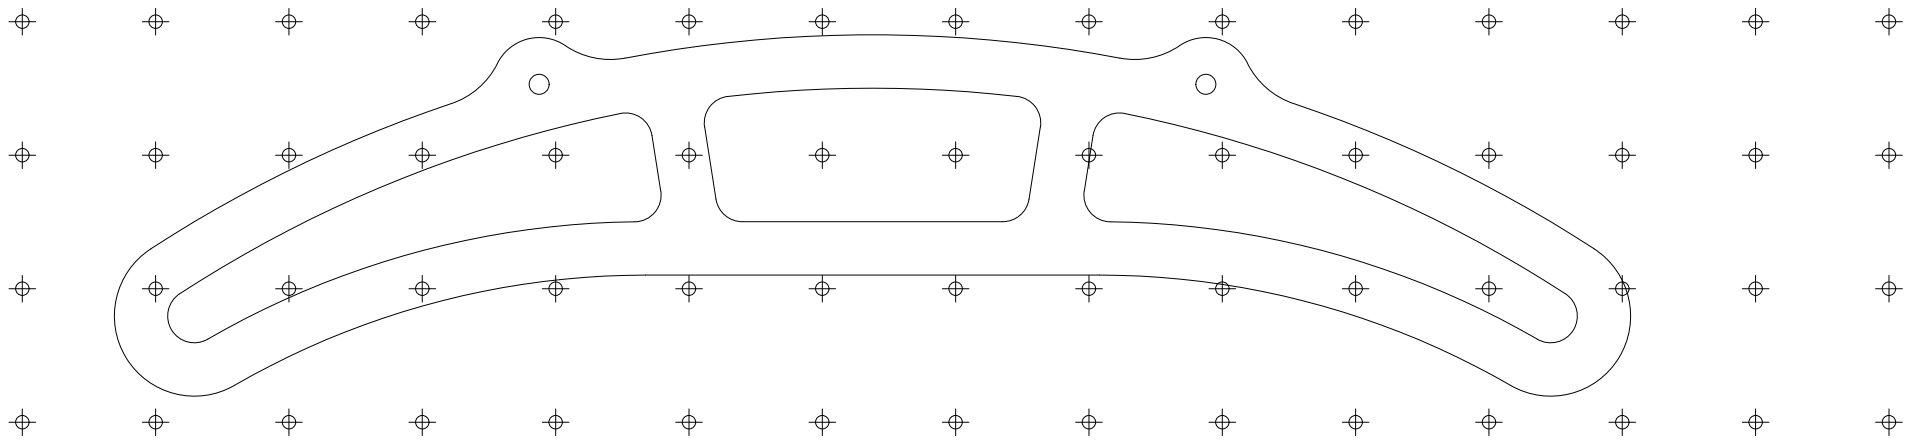
[picture p49: page 2]
