patrickiel/pull-up-bar/cad/pull-up bar variants/biacromia breadth 46 cm (18.1 inch).pdf

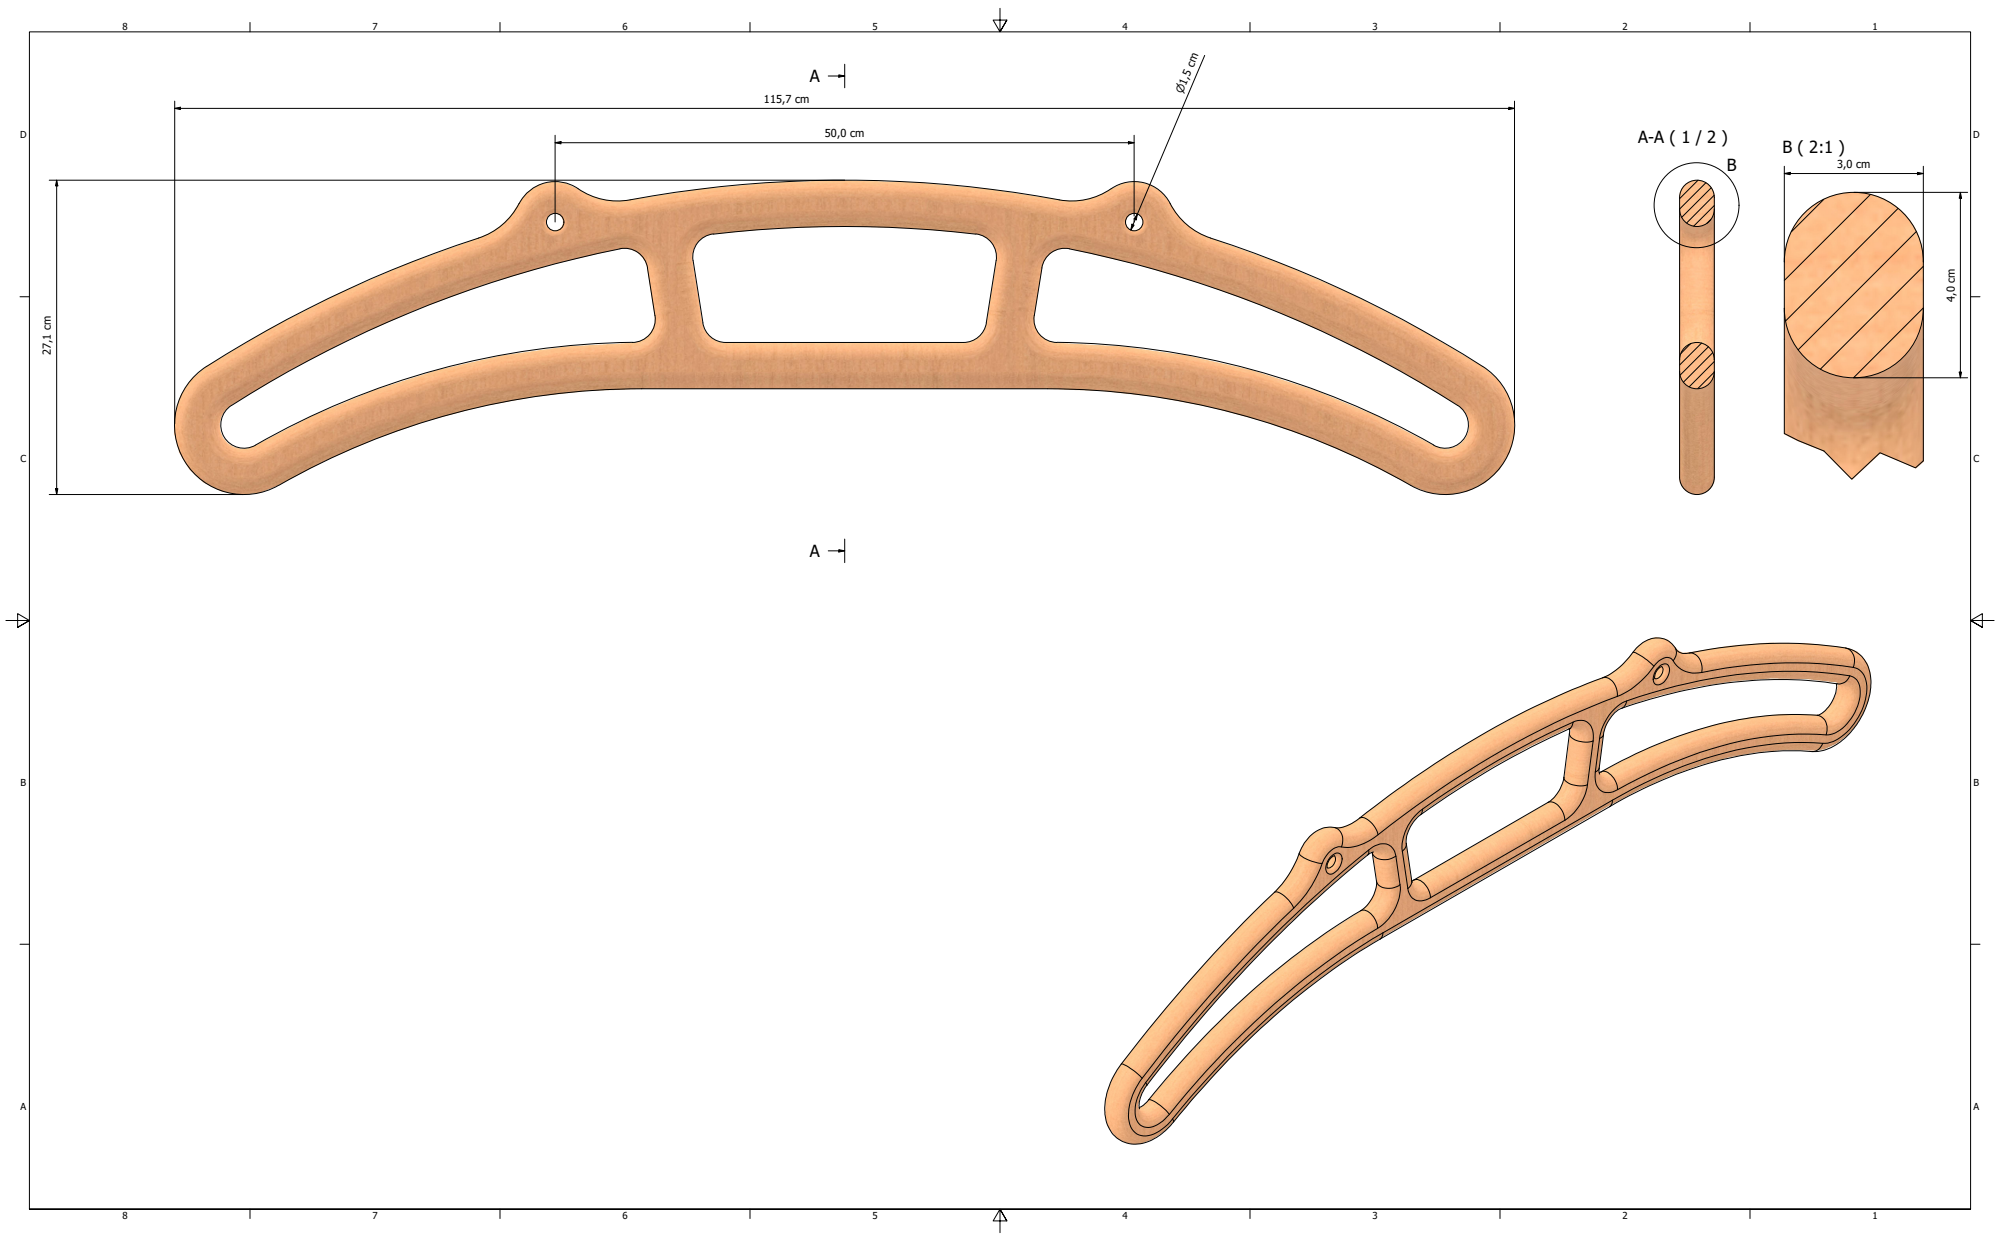
[picture p50: page 1]

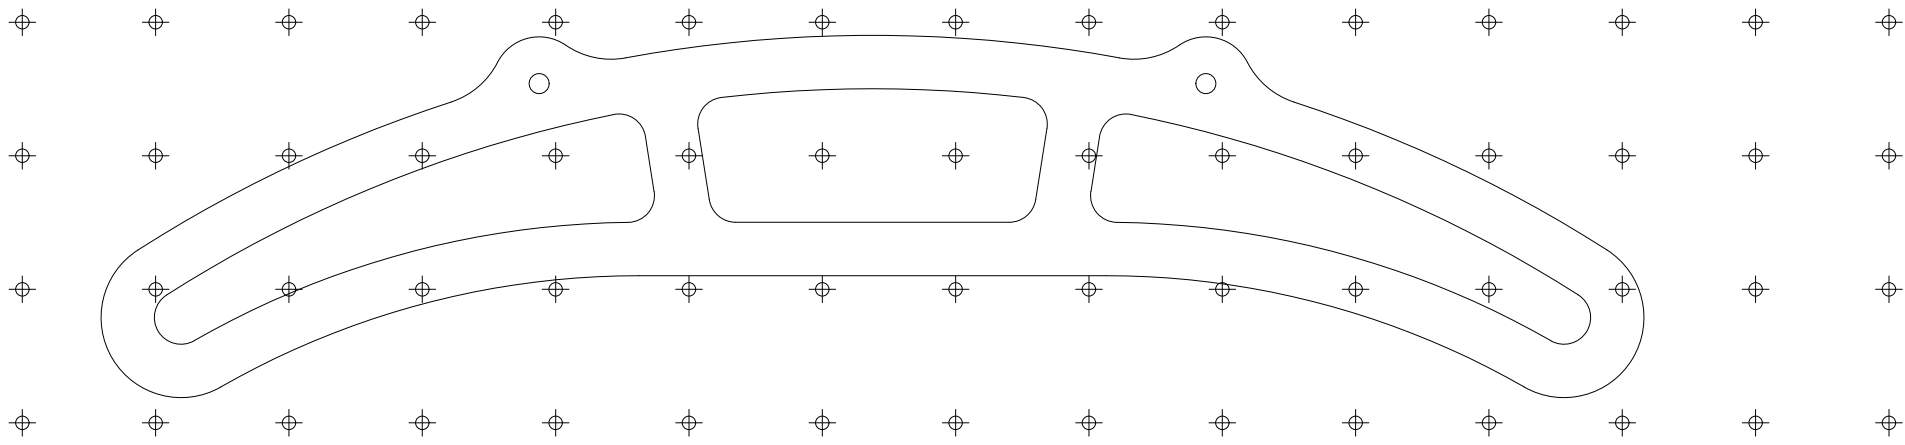
[picture p51: page 2]
