patrickiel/pull-up-bar/cad/pull-up bar variants/biacromia breadth 47 cm (18.5 inch).pdf

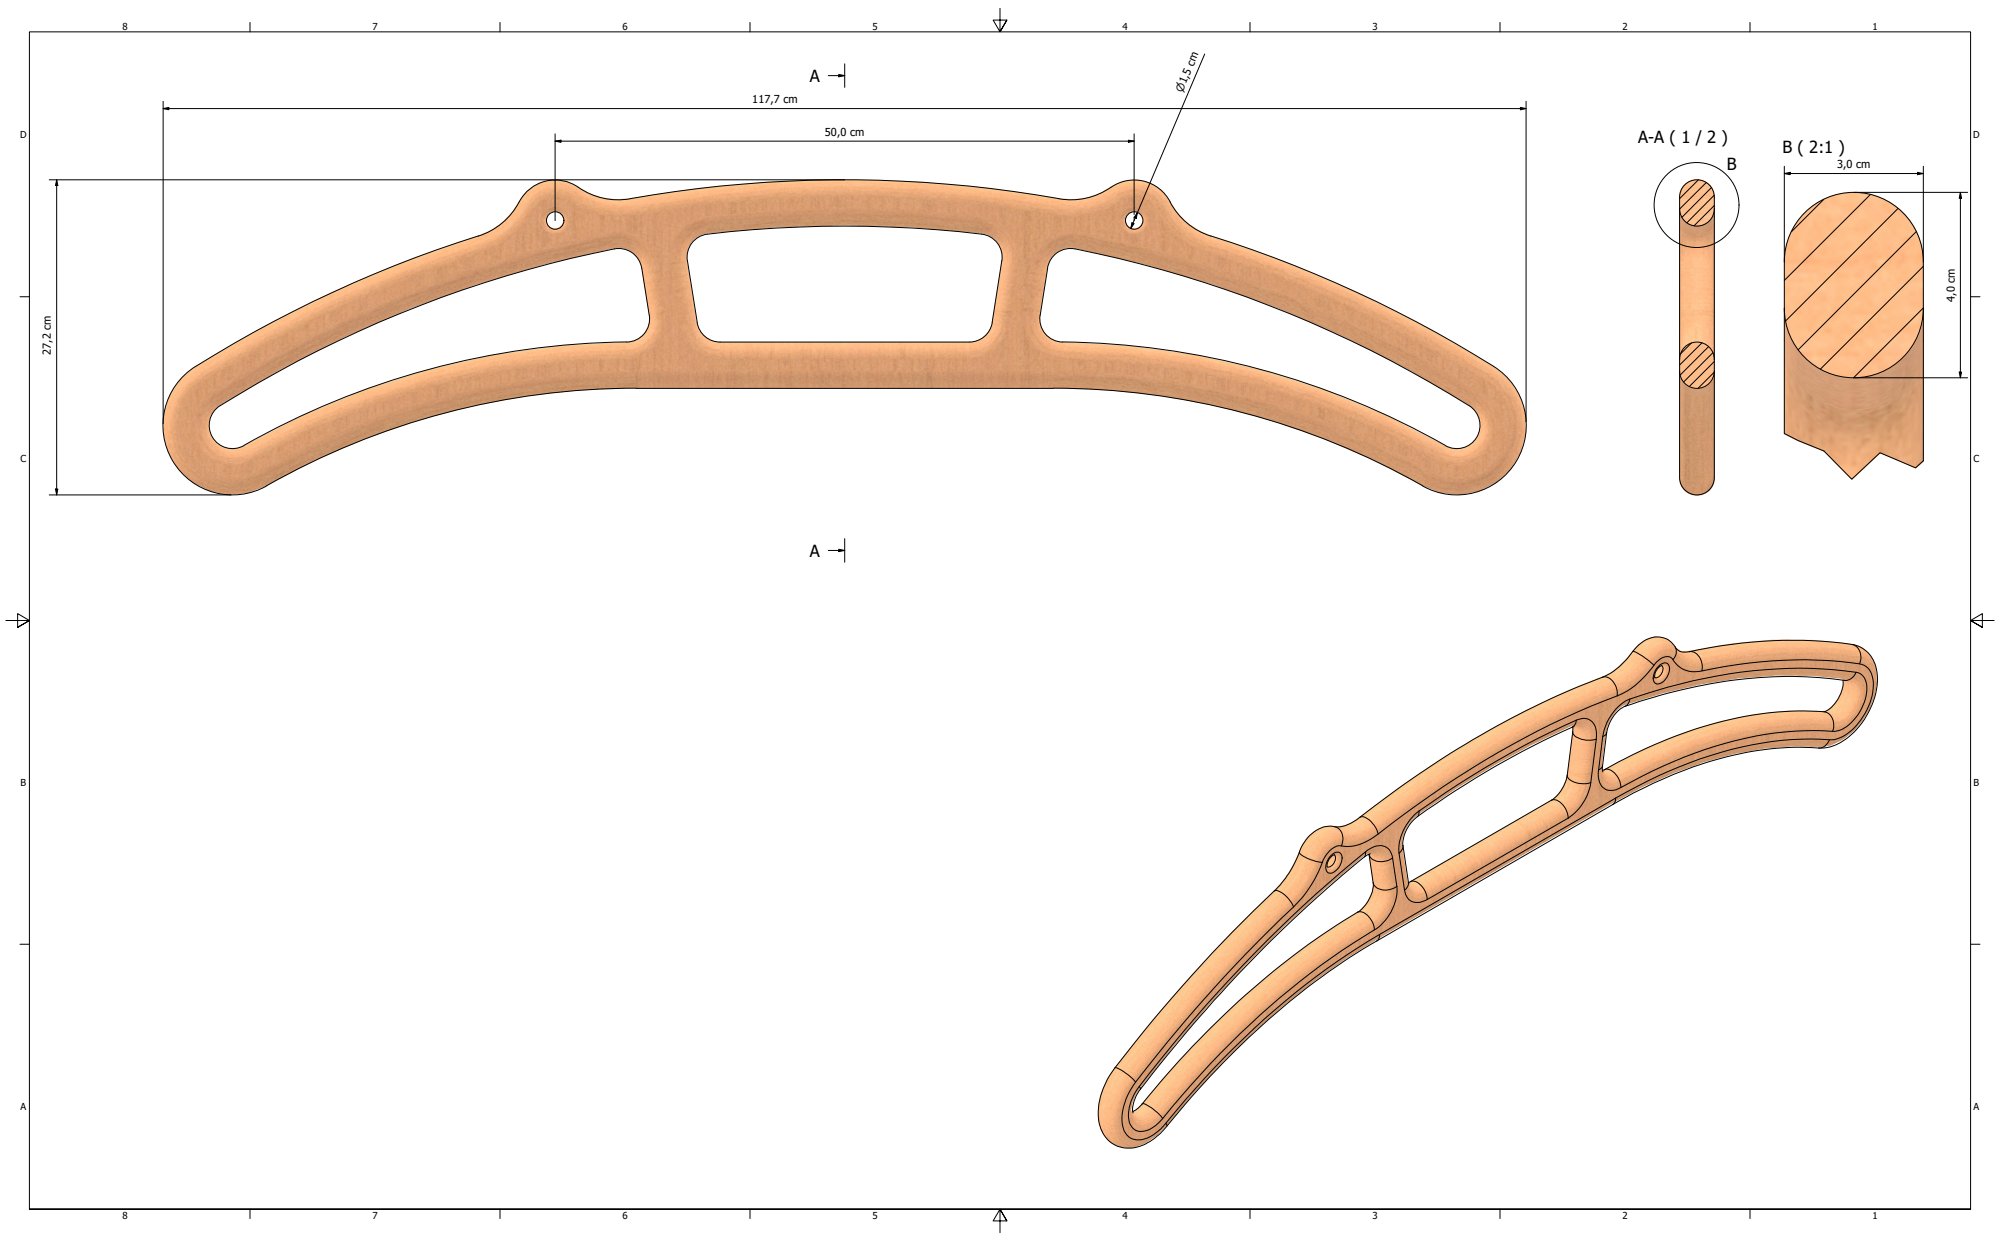
[picture p52: page 1]

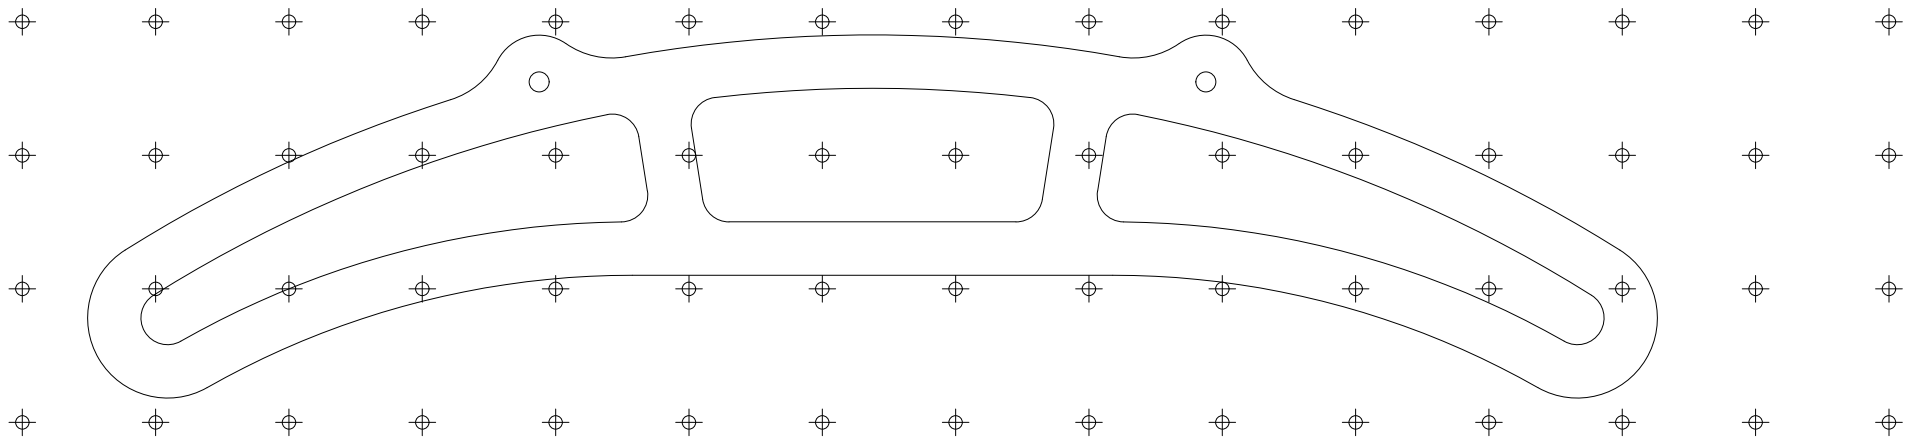
[picture p53: page 2]
