patrickiel/pull-up-bar/cad/pull-up bar variants/biacromia breadth 48 cm (18.9 inch).pdf

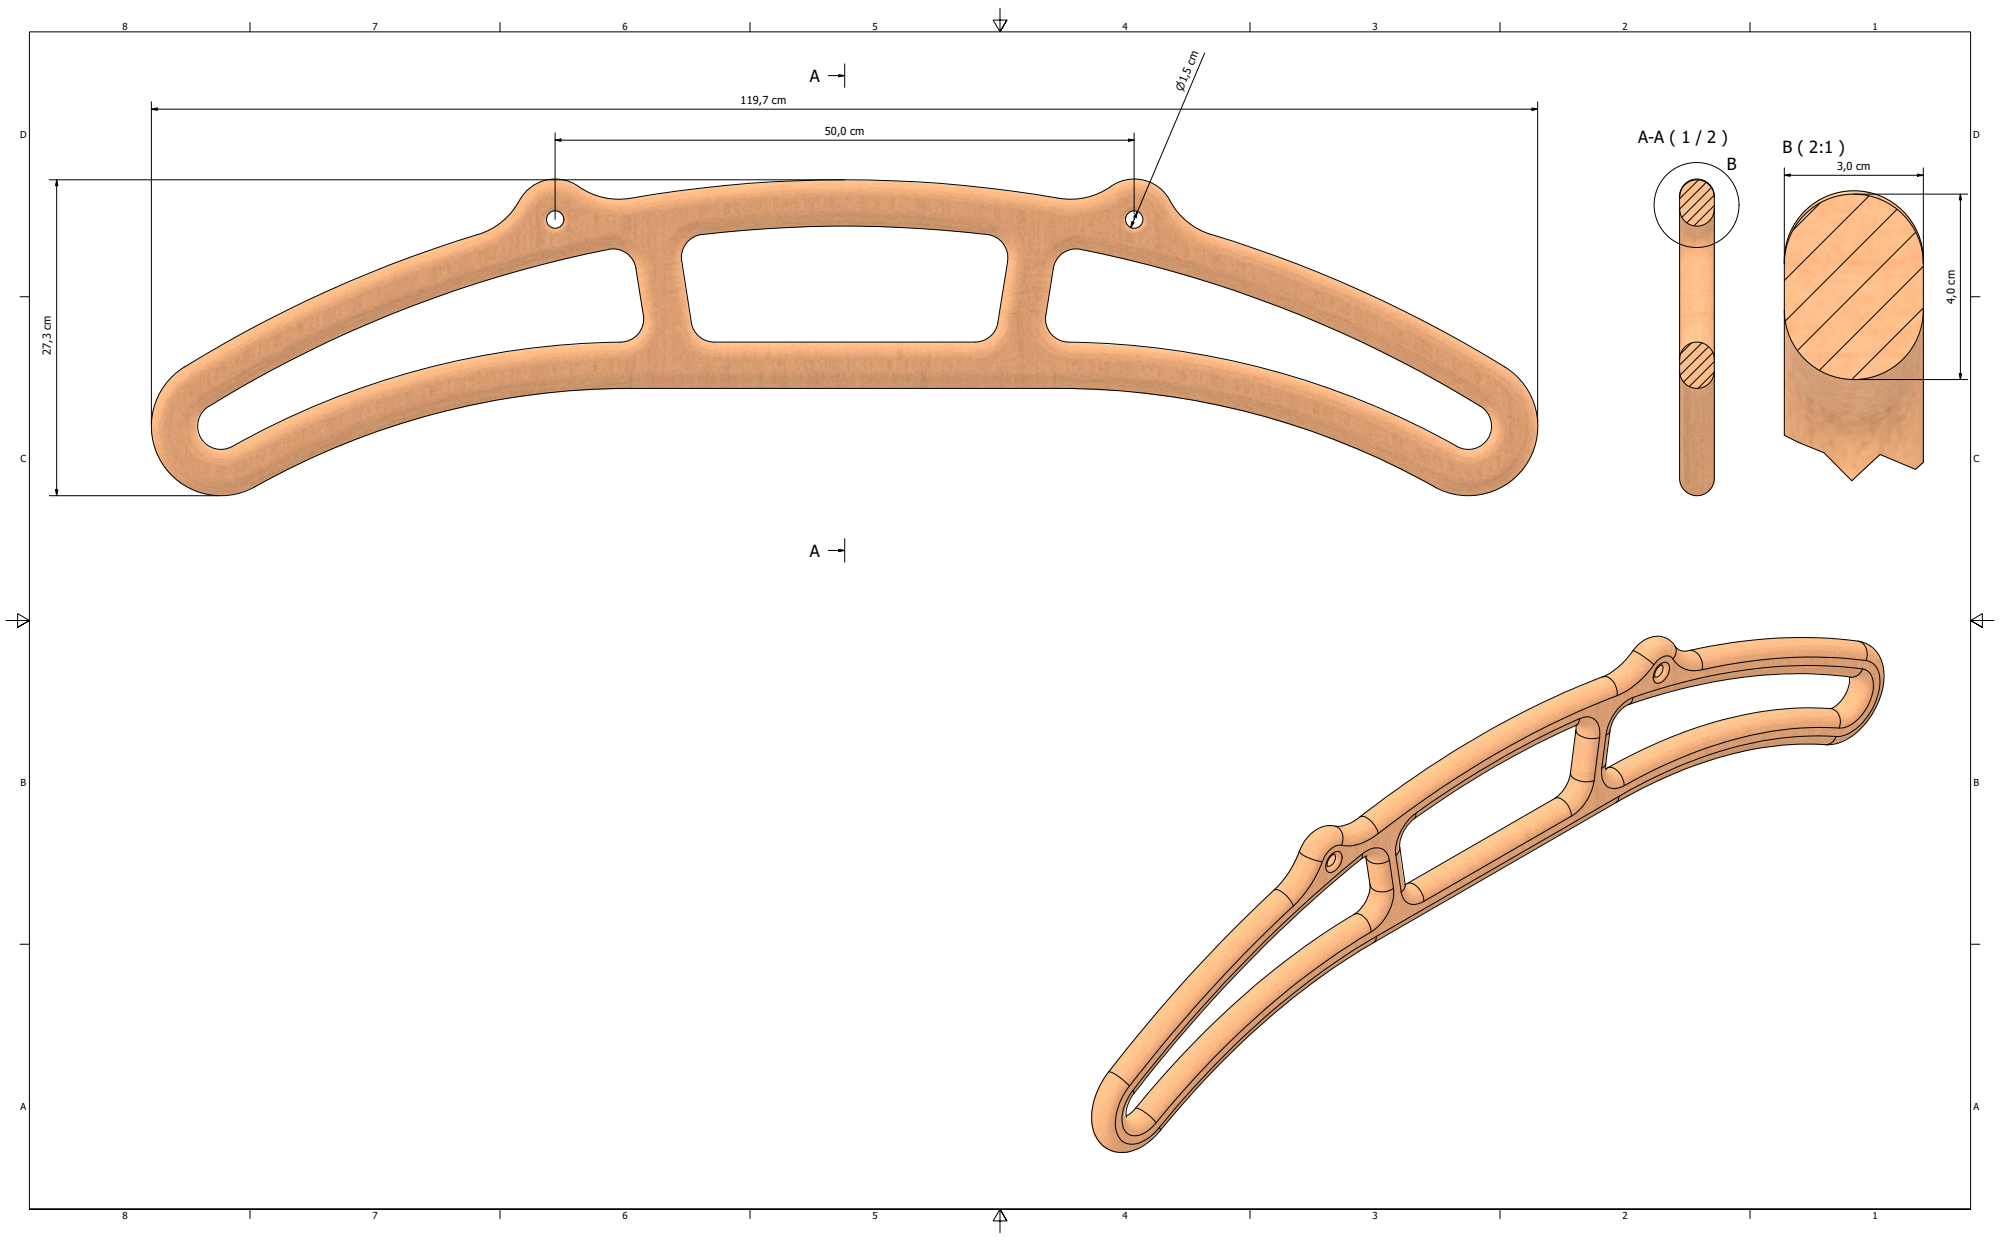
[picture p54: page 1]

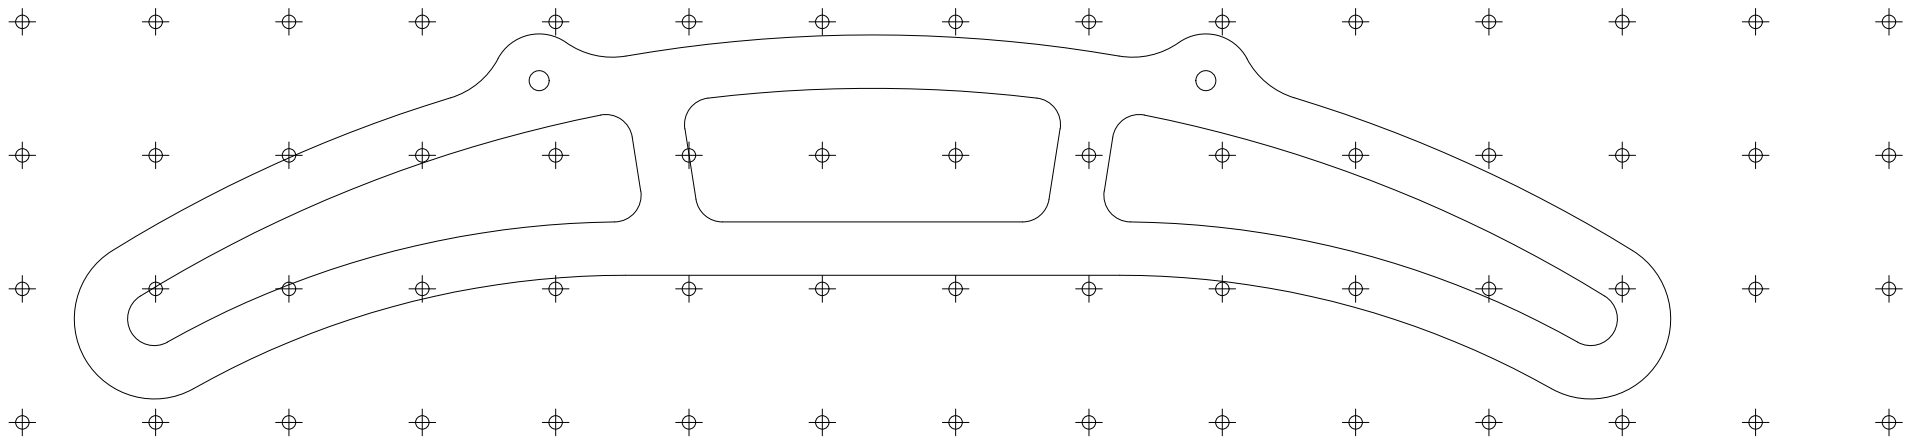
[picture p55: page 2]
