patrickiel/pull-up-bar/cad/pull-up bar variants/biacromia breadth 49 cm (19.3 inch).pdf

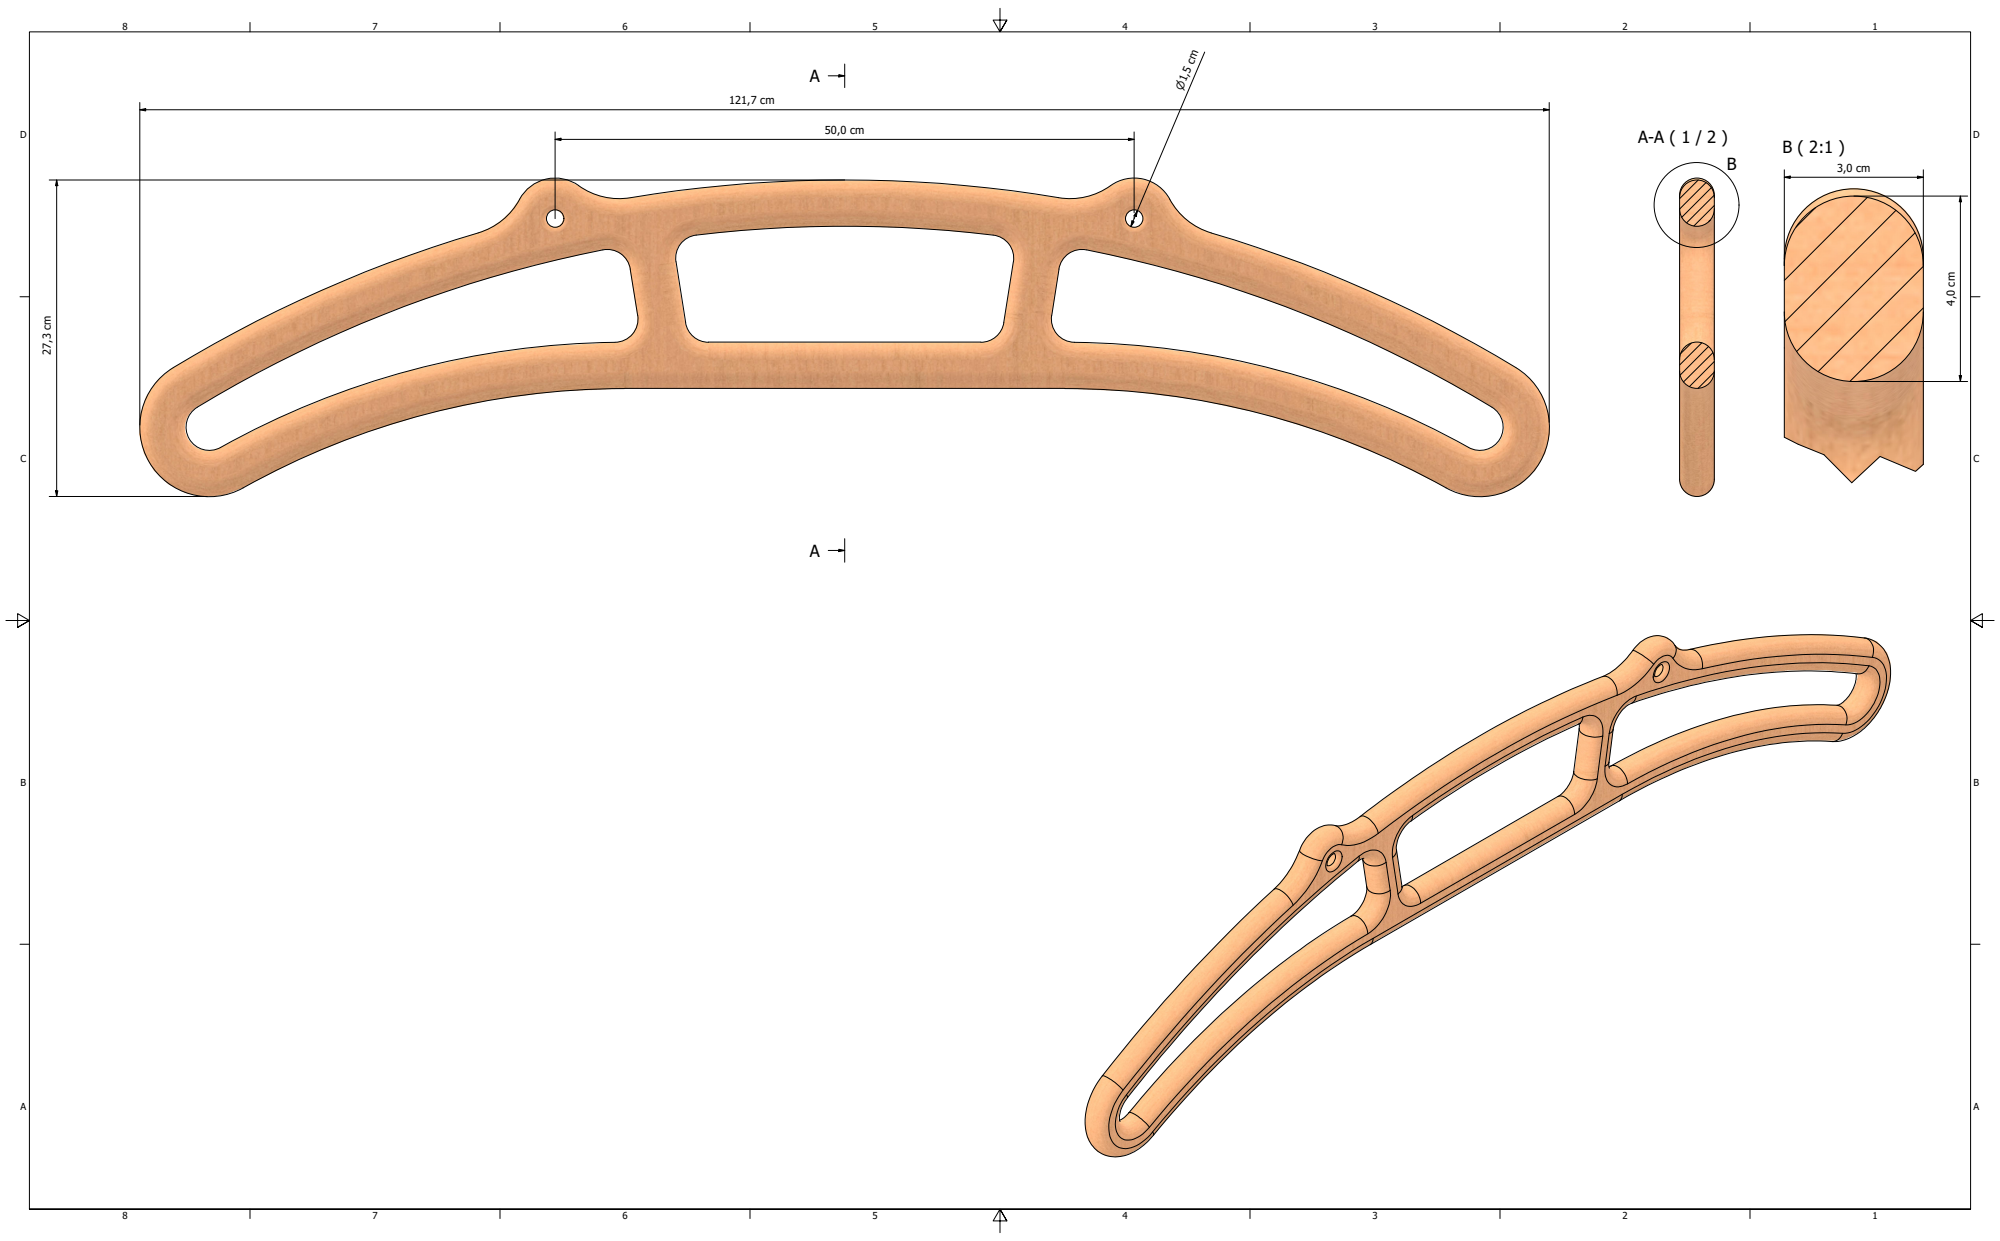
[picture p56: page 1]

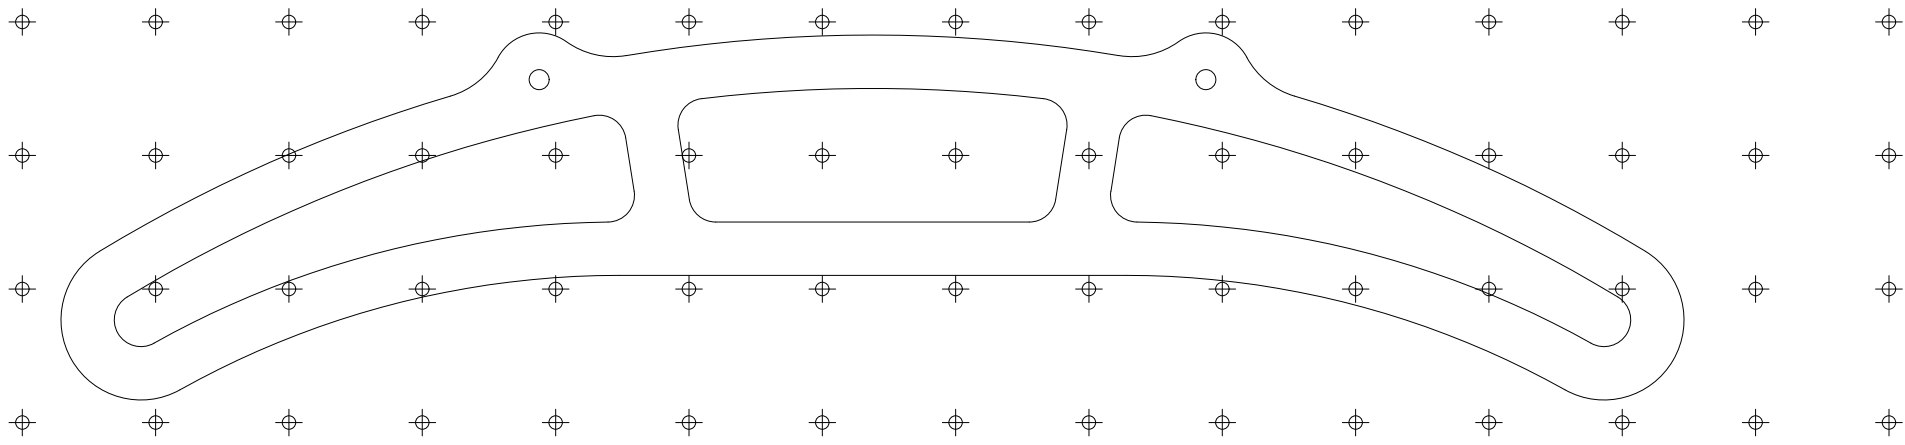
[picture p57: page 2]
