patrickiel/pull-up-bar/cad/pull-up bar variants/biacromia breadth 50 cm (19.7 inch).pdf

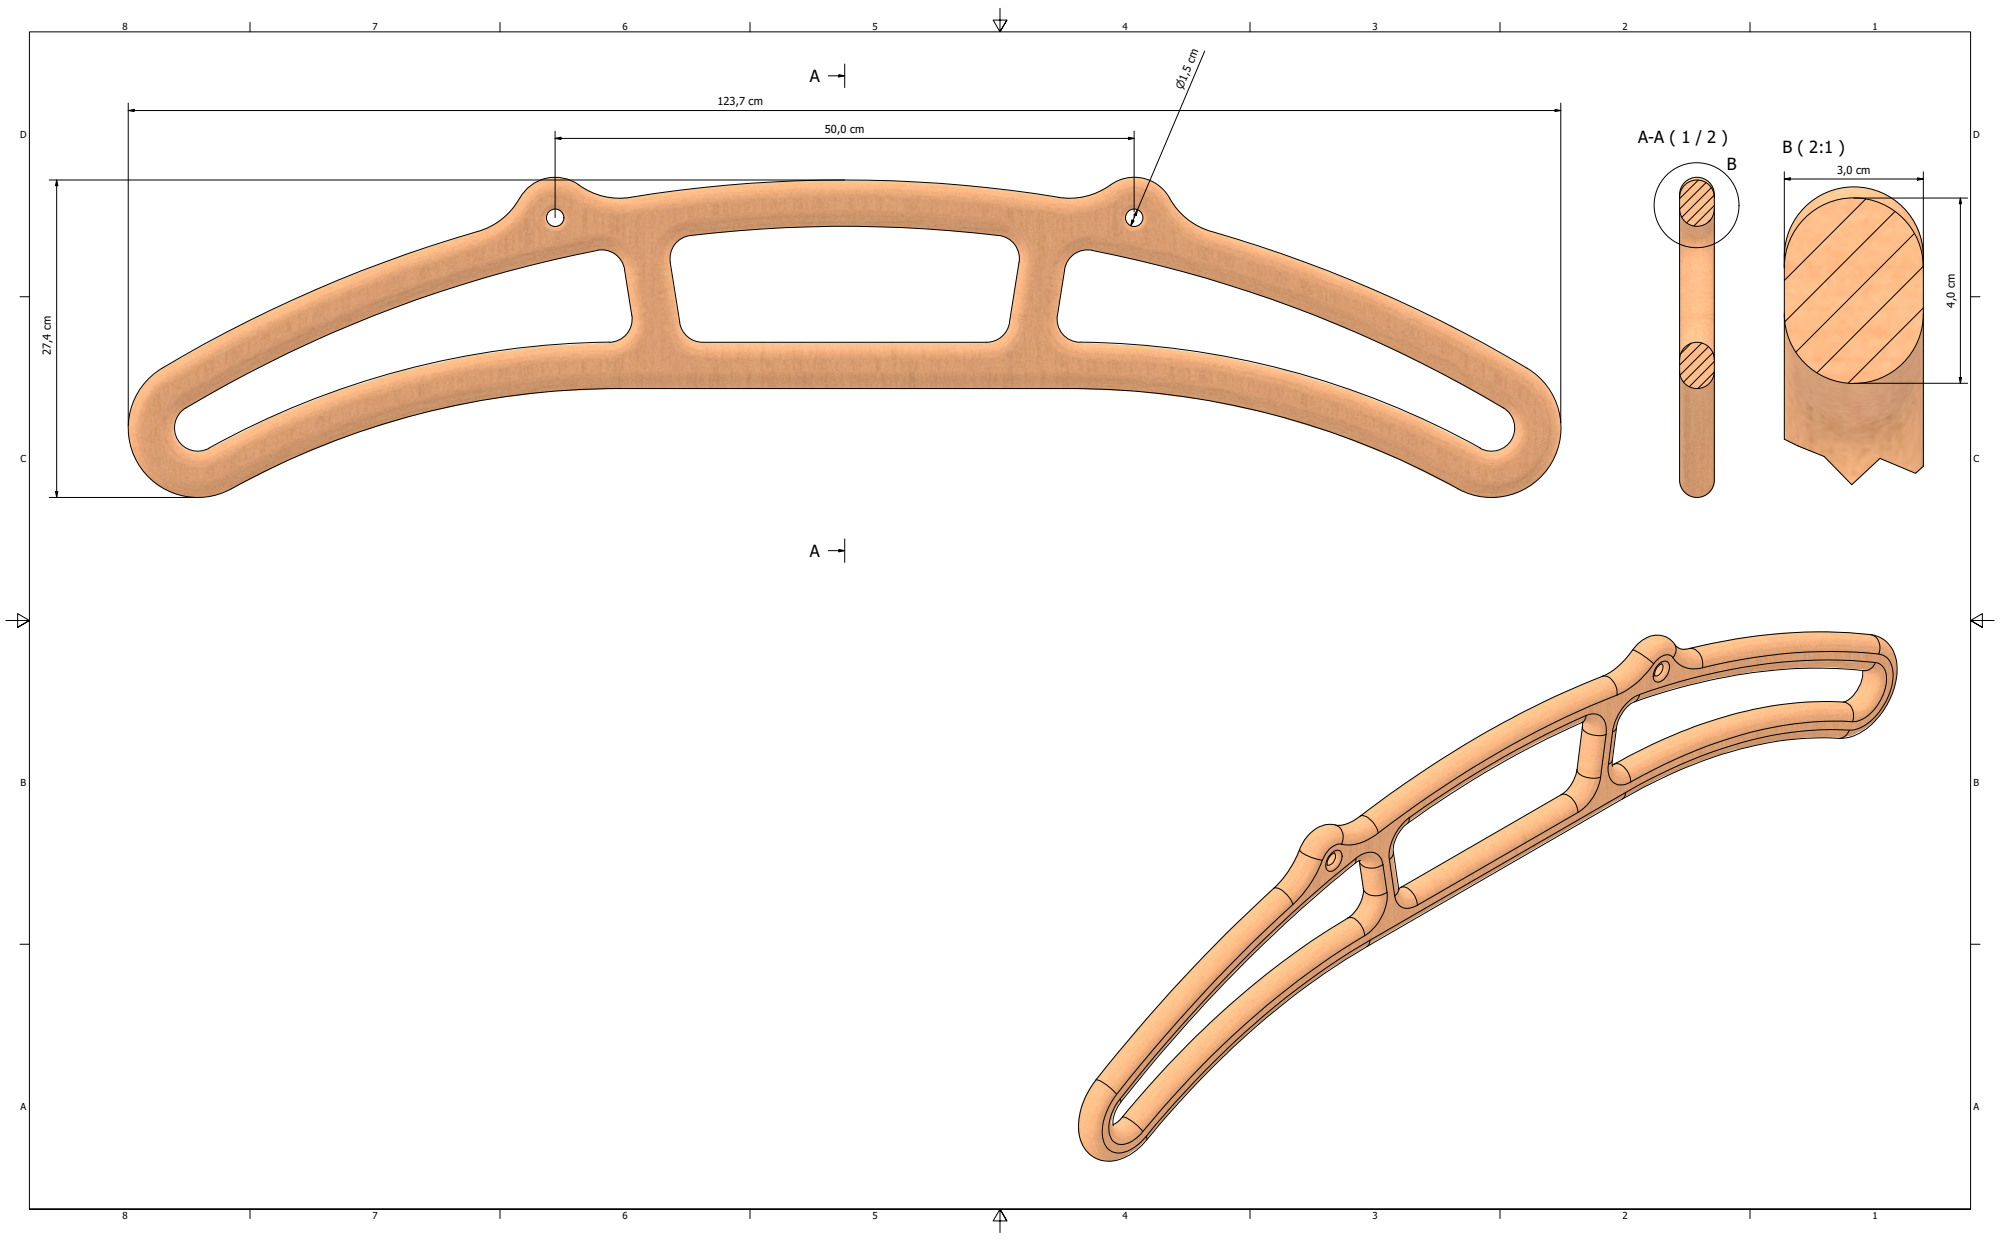
[picture p58: page 1]

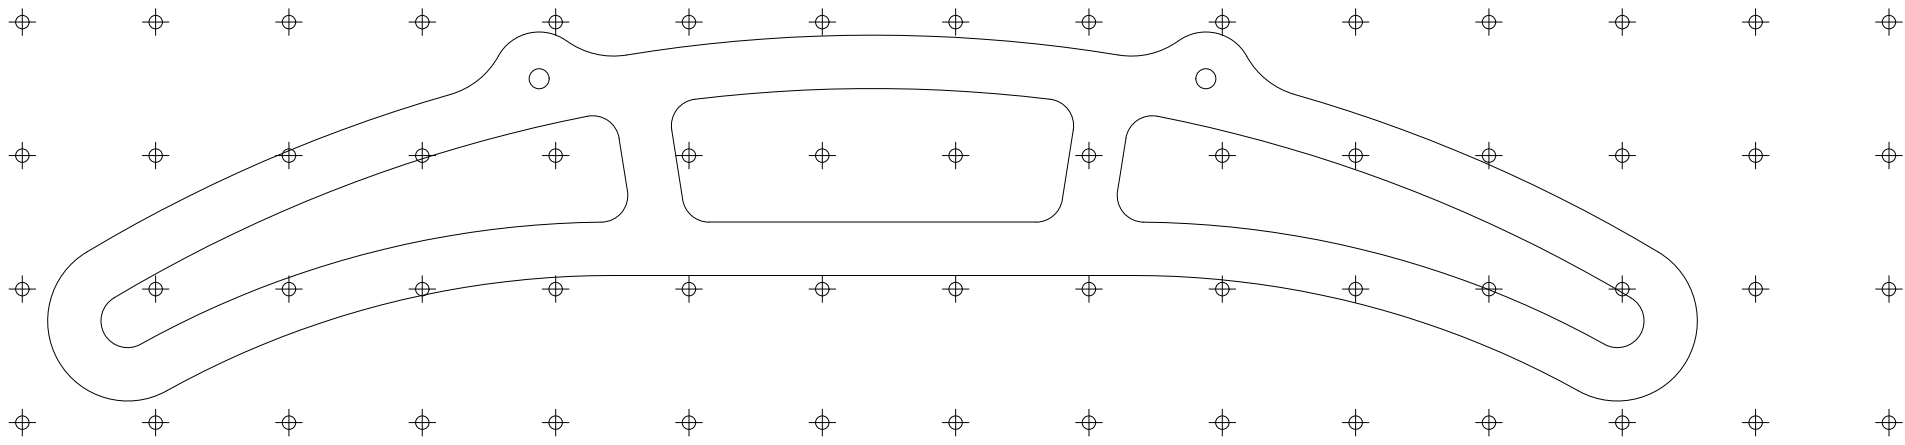
[picture p59: page 2]
