patrickiel/pull-up-bar/cad/pull-up bar variants/biacromia breadth 51 cm (20.1 inch).pdf

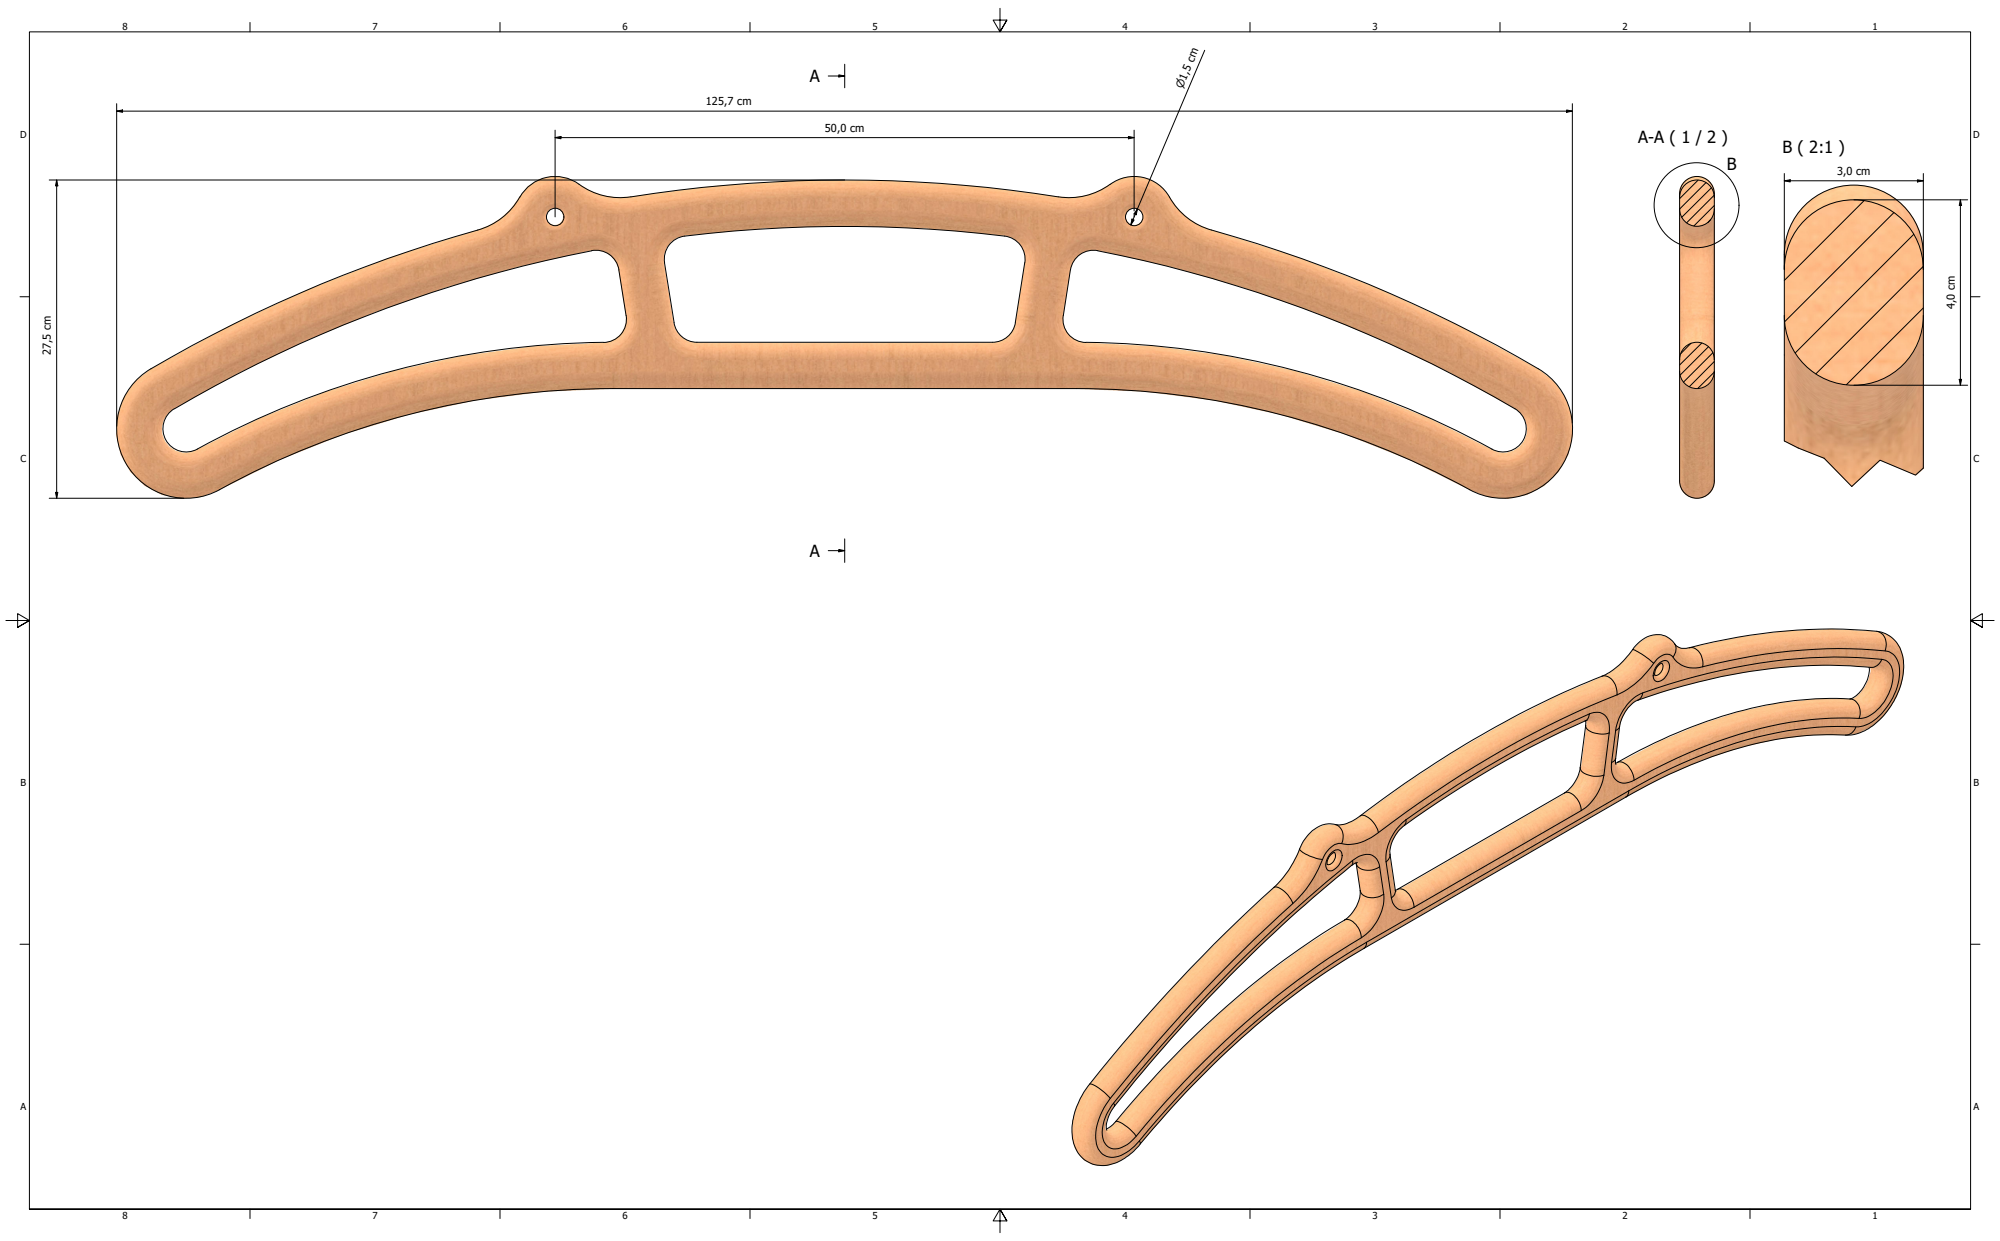
[picture p60: page 1]

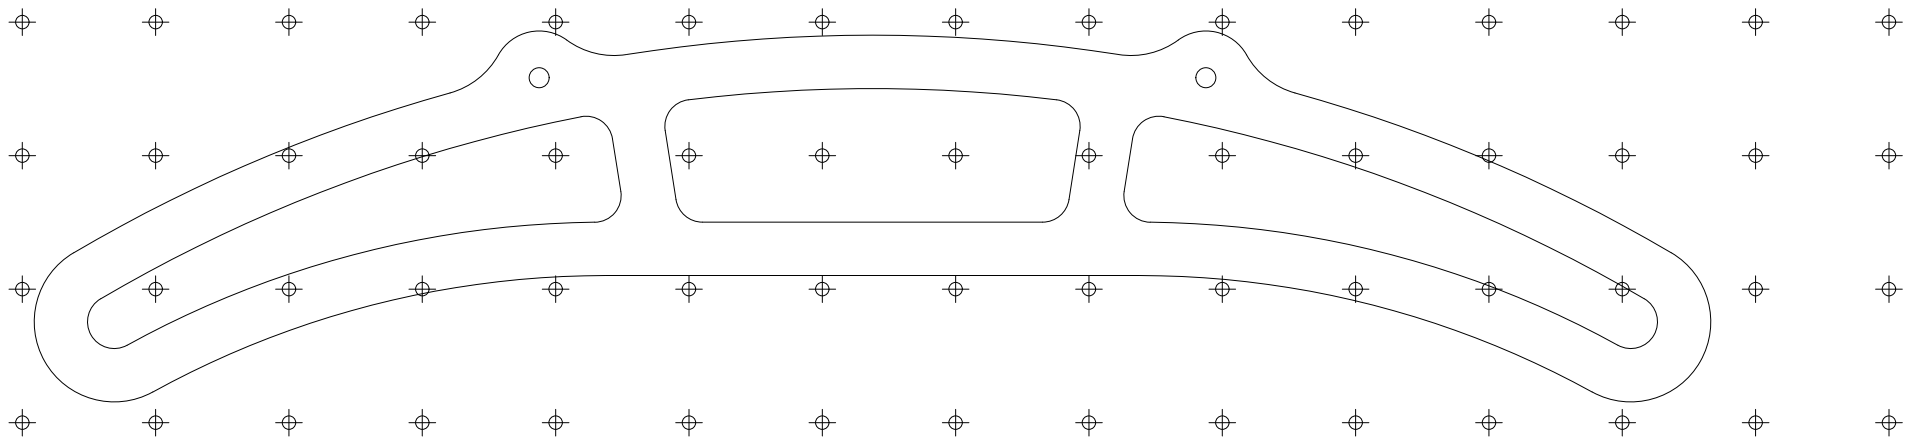
[picture p61: page 2]
