patrickiel/pull-up-bar/cad/pull-up bar variants/biacromia breadth 52 cm (20.5 inch).pdf

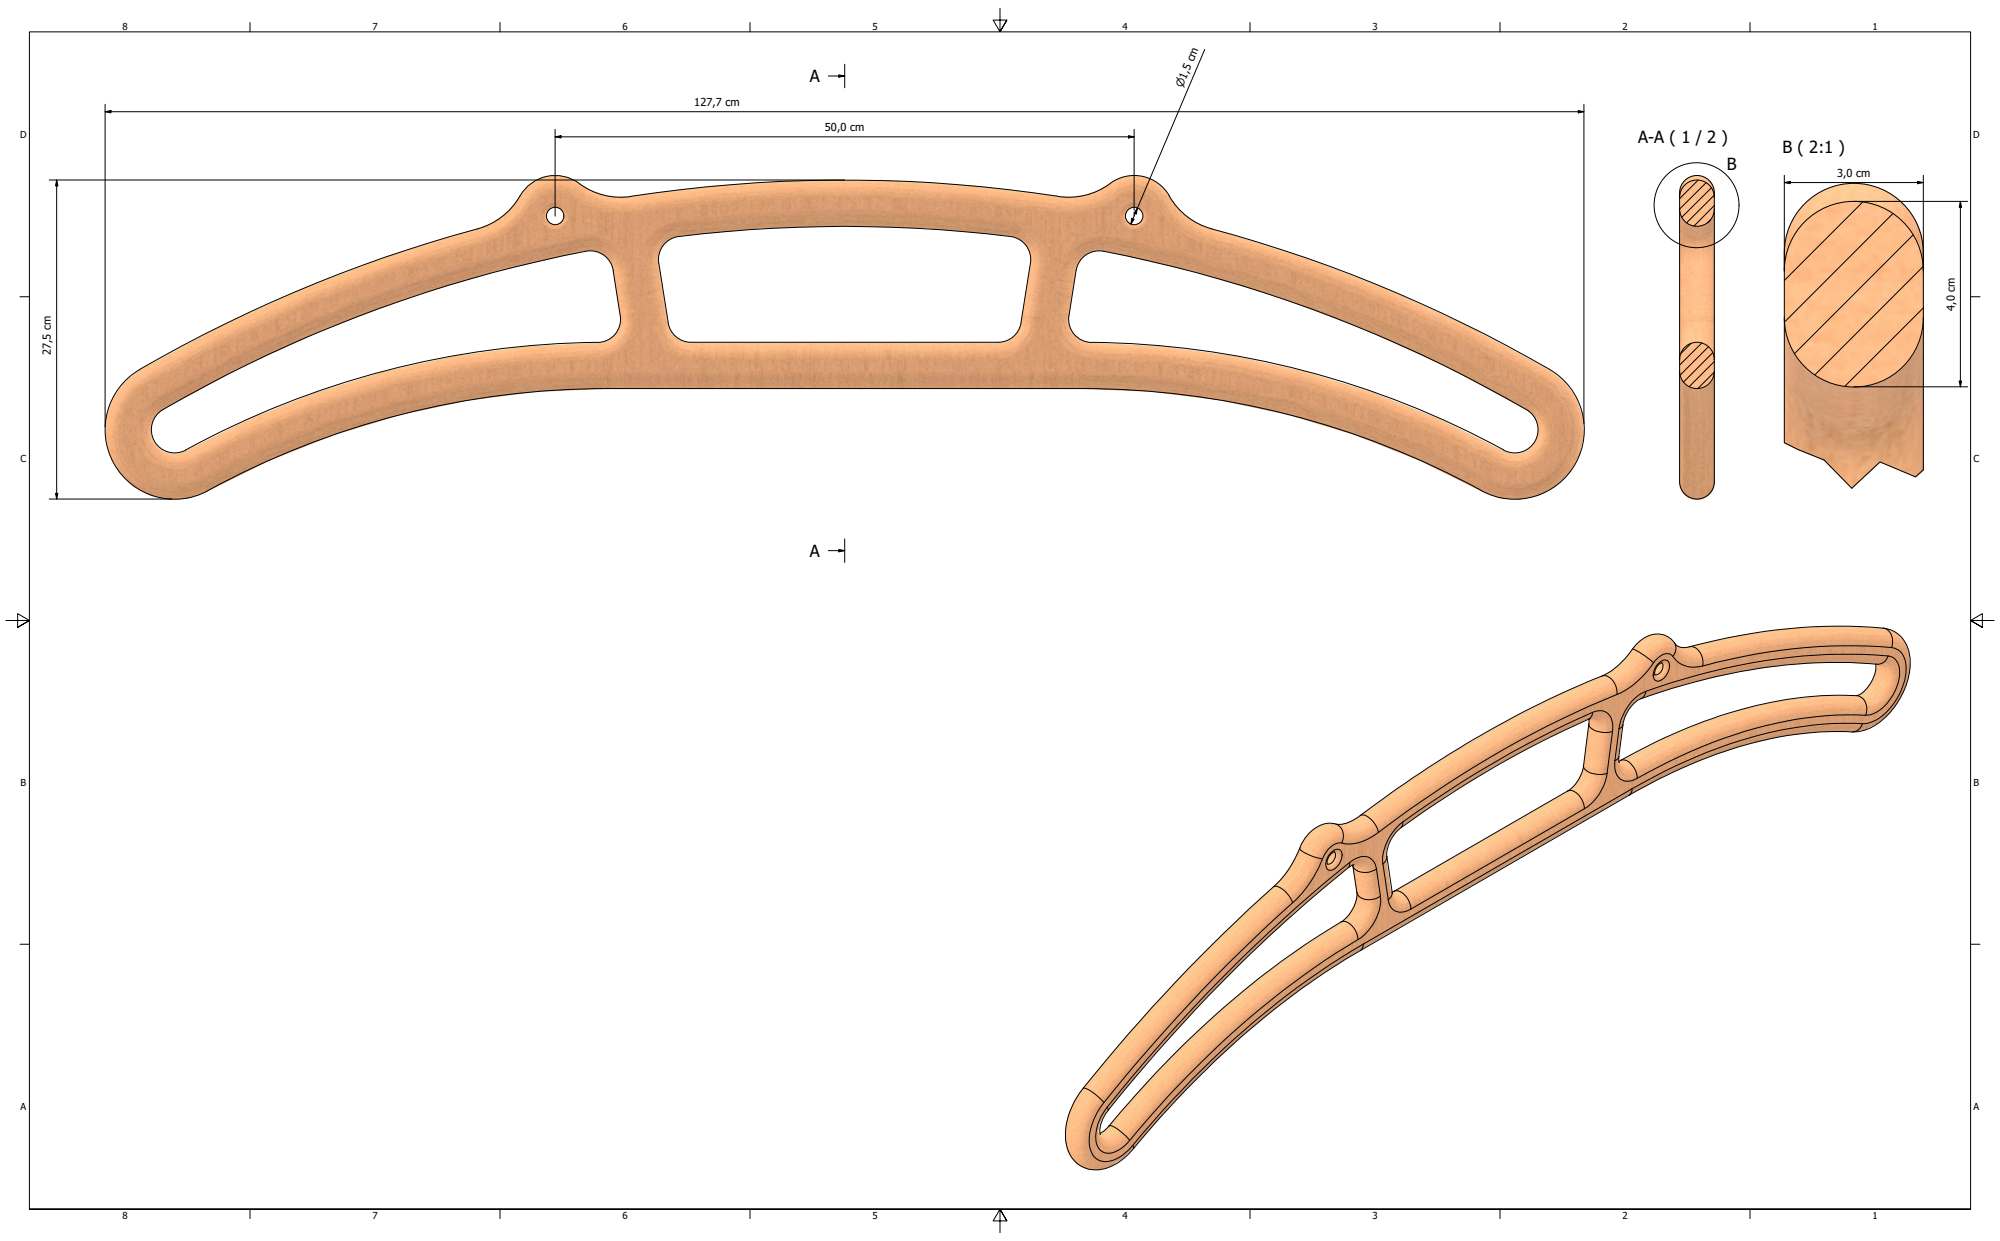
[picture p62: page 1]

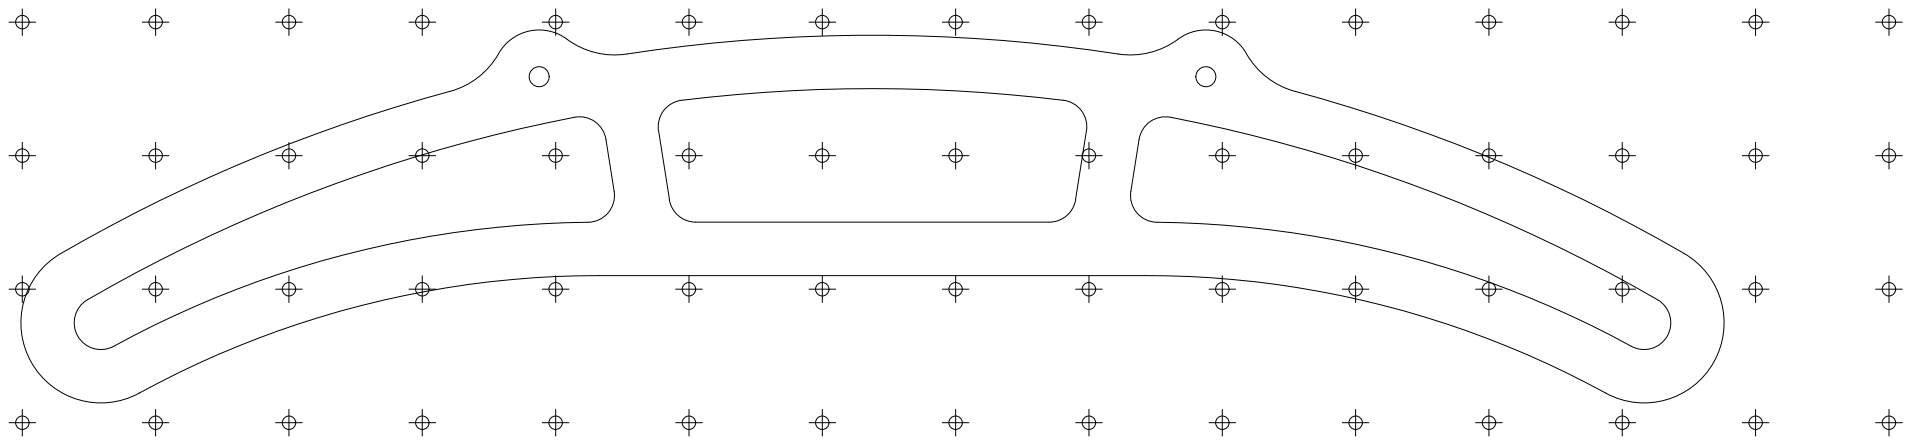
[picture p63: page 2]
