patrickiel/pull-up-bar/cad/pull-up bar variants/biacromia breadth 53 cm (20.9 inch).pdf

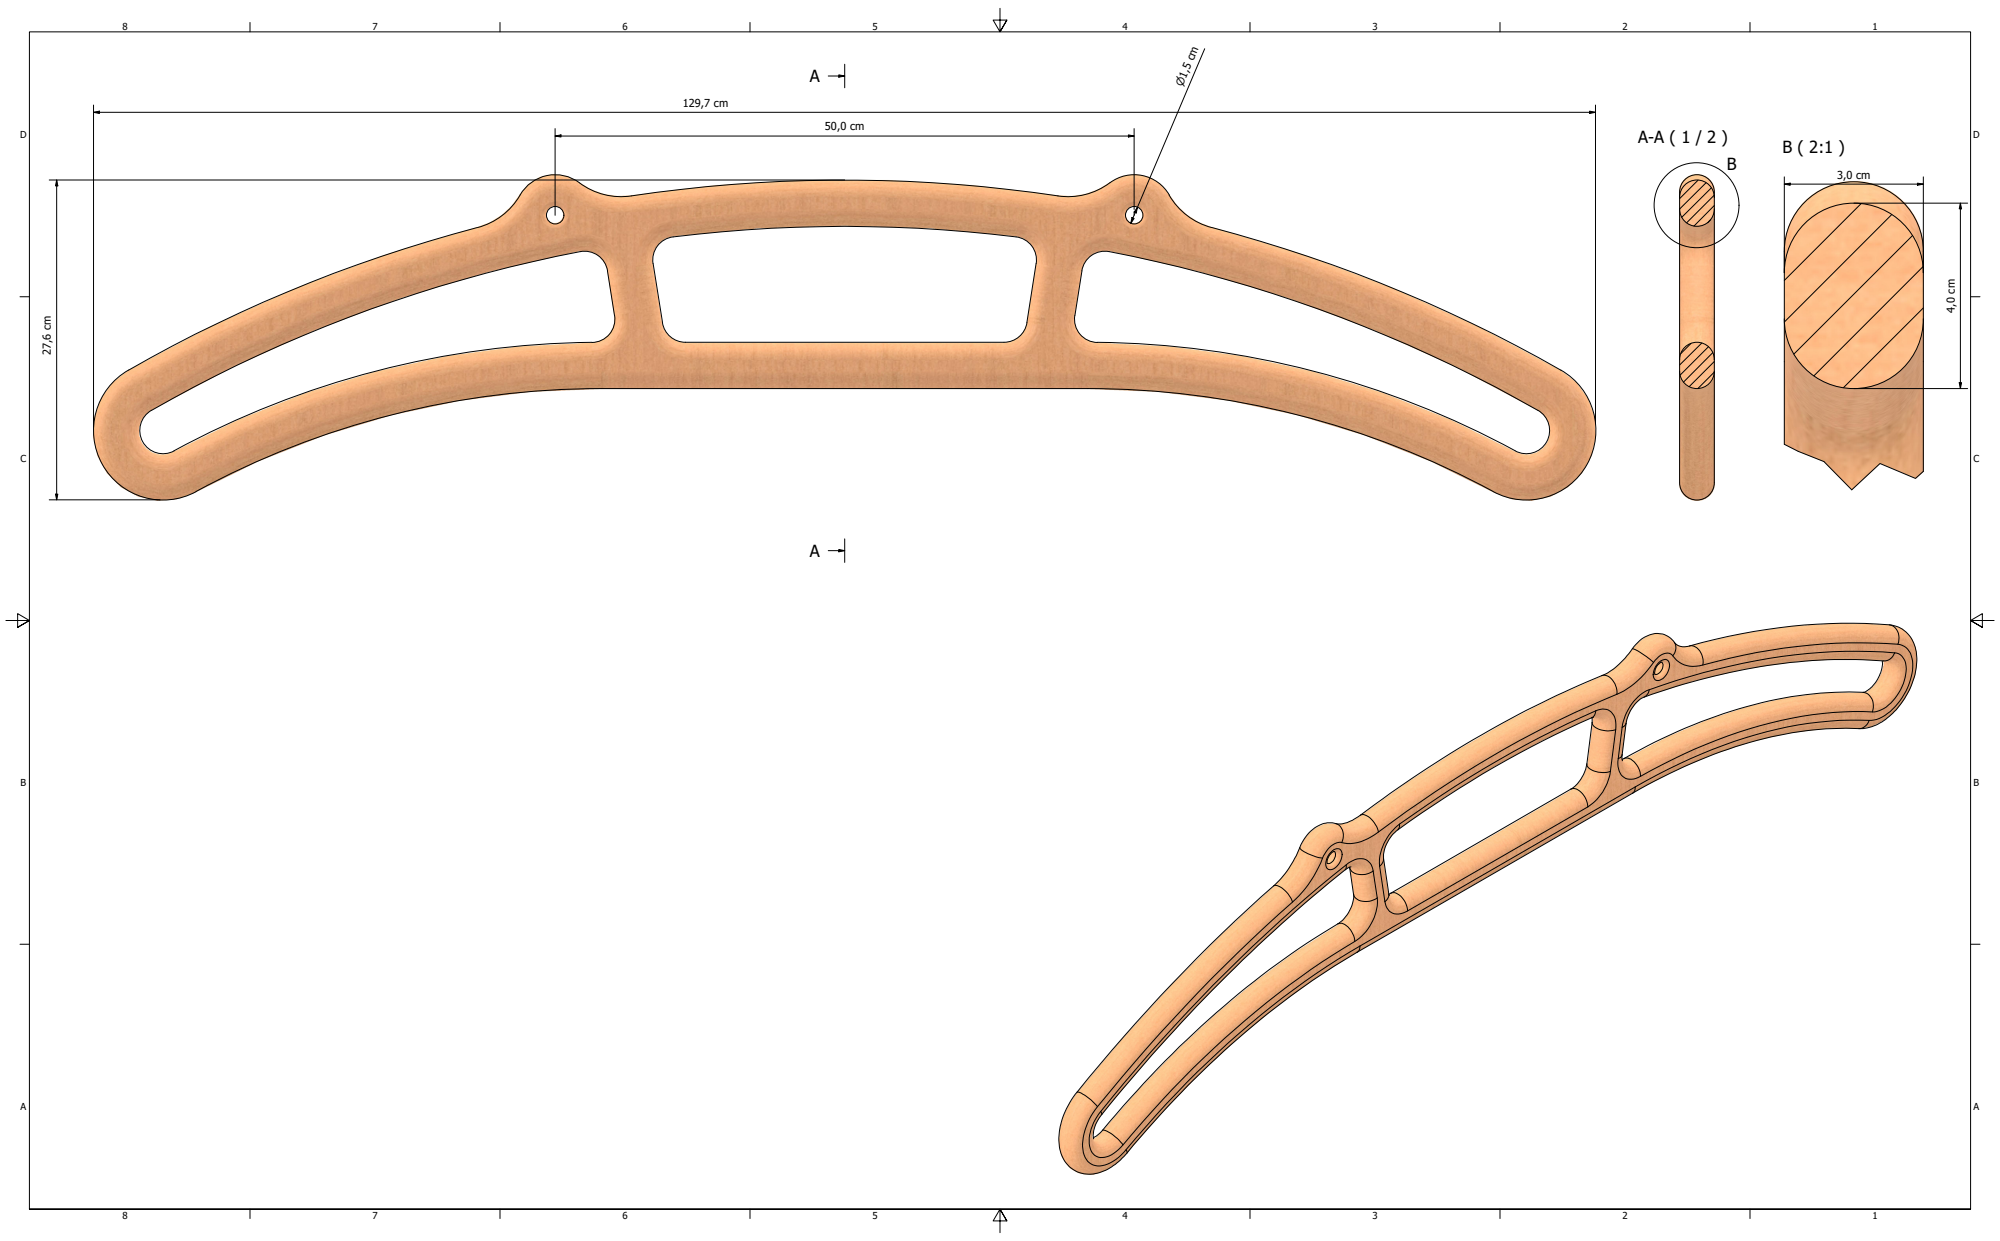
[picture p64: page 1]

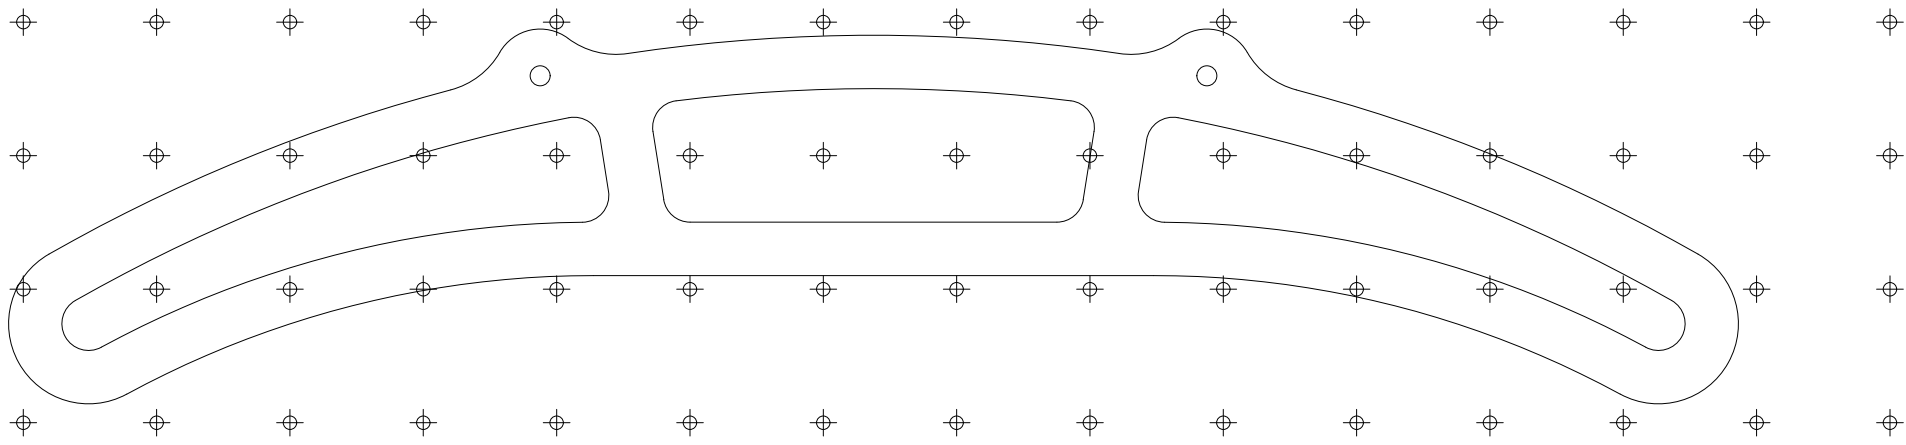
[picture p65: page 2]
