patrickiel/pull-up-bar/cad/pull-up bar variants/biacromia breadth 54 cm (21.3 inch).pdf

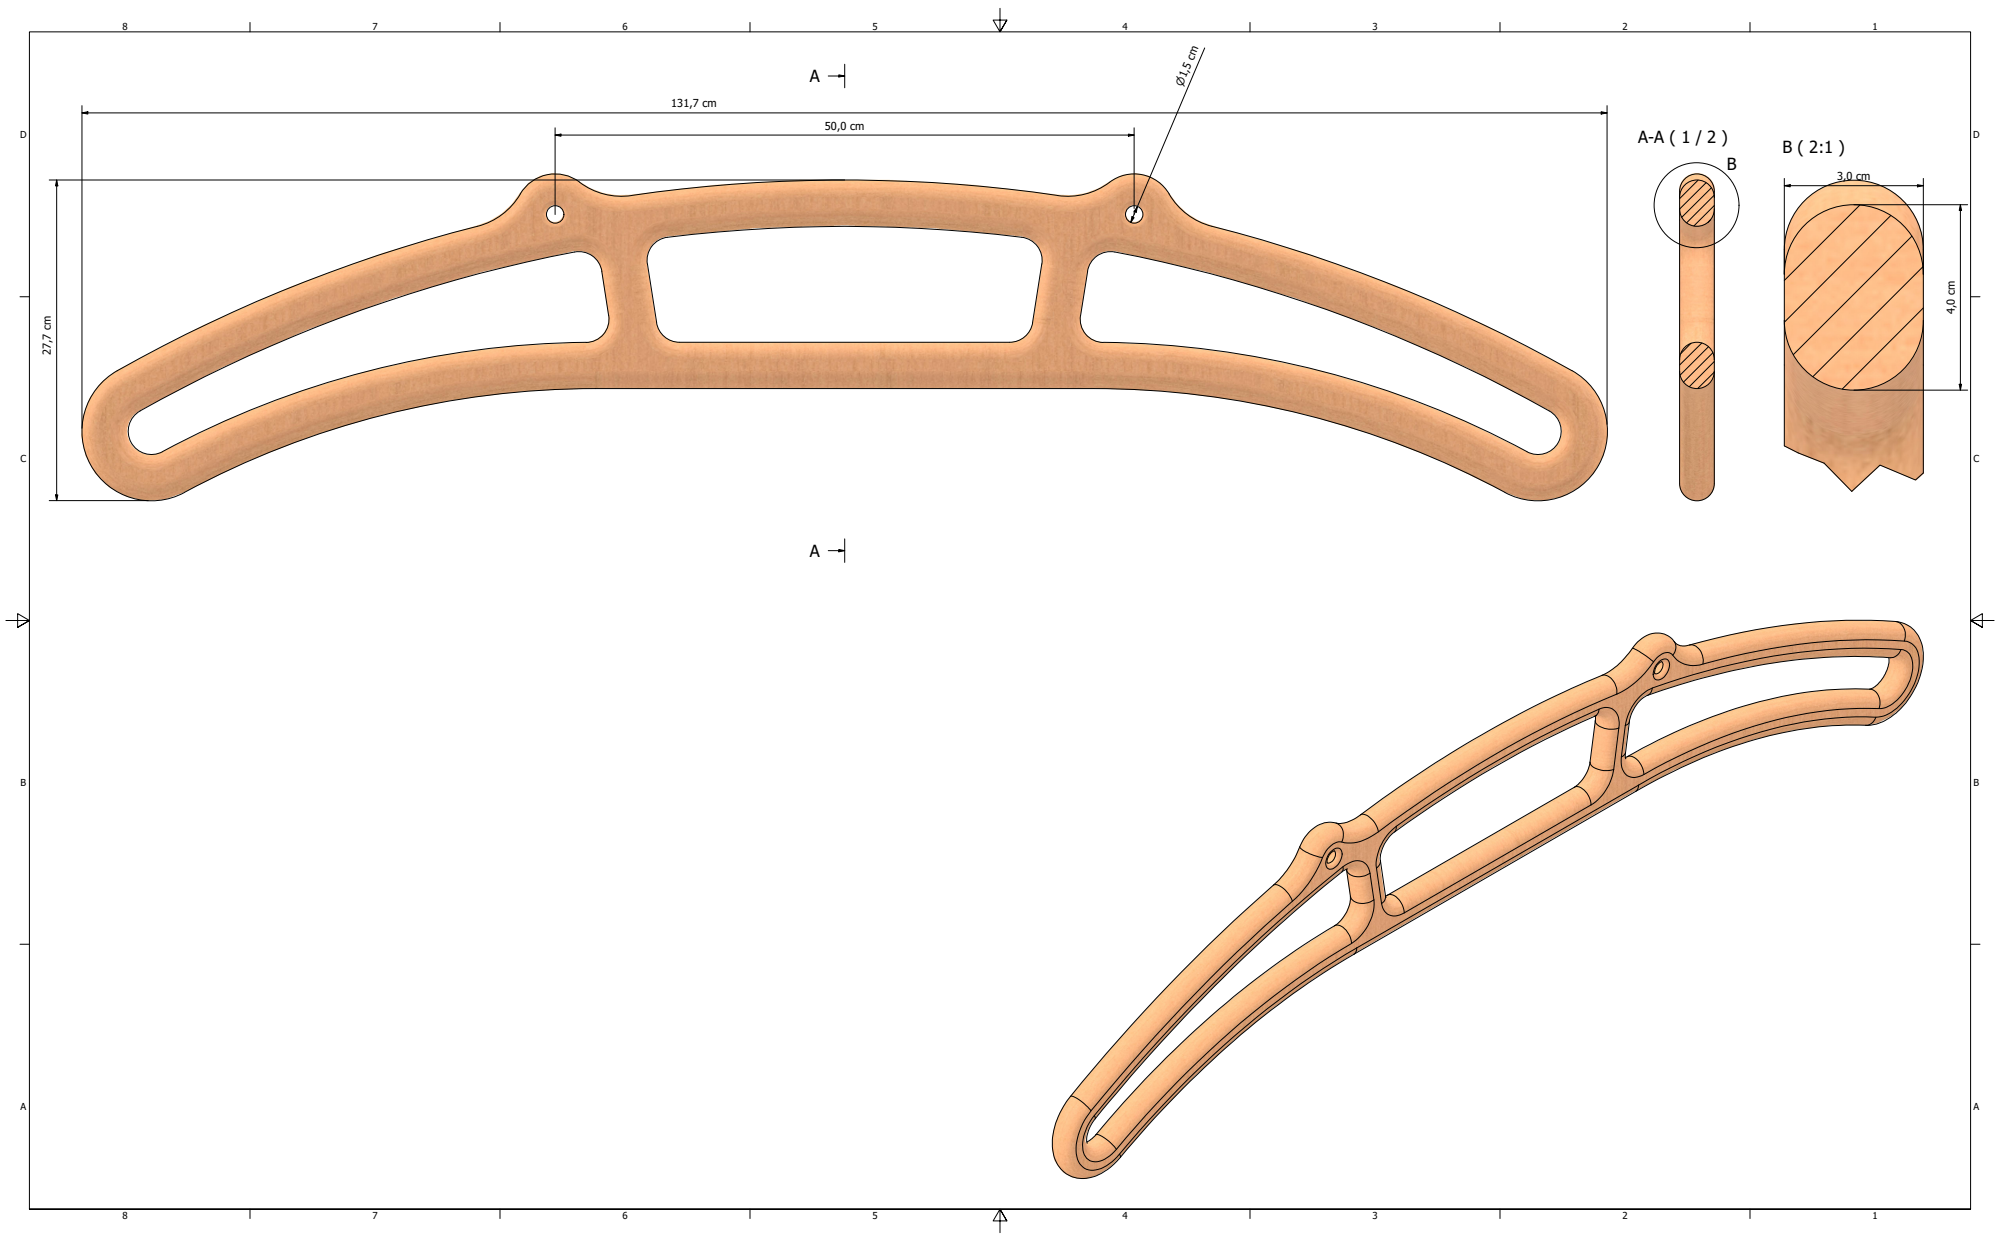
[picture p66: page 1]

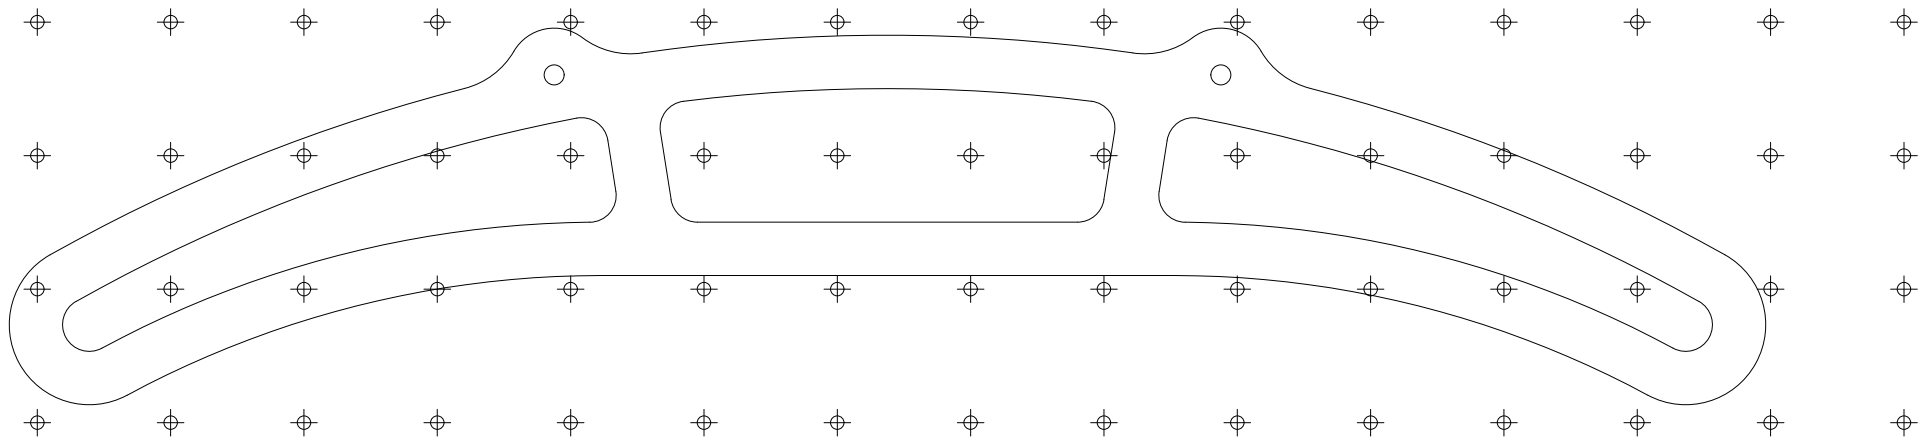
[picture p67: page 2]
