patrickiel/pull-up-bar/cad/pull-up bar variants/biacromia breadth 55 cm (21.7 inch).pdf

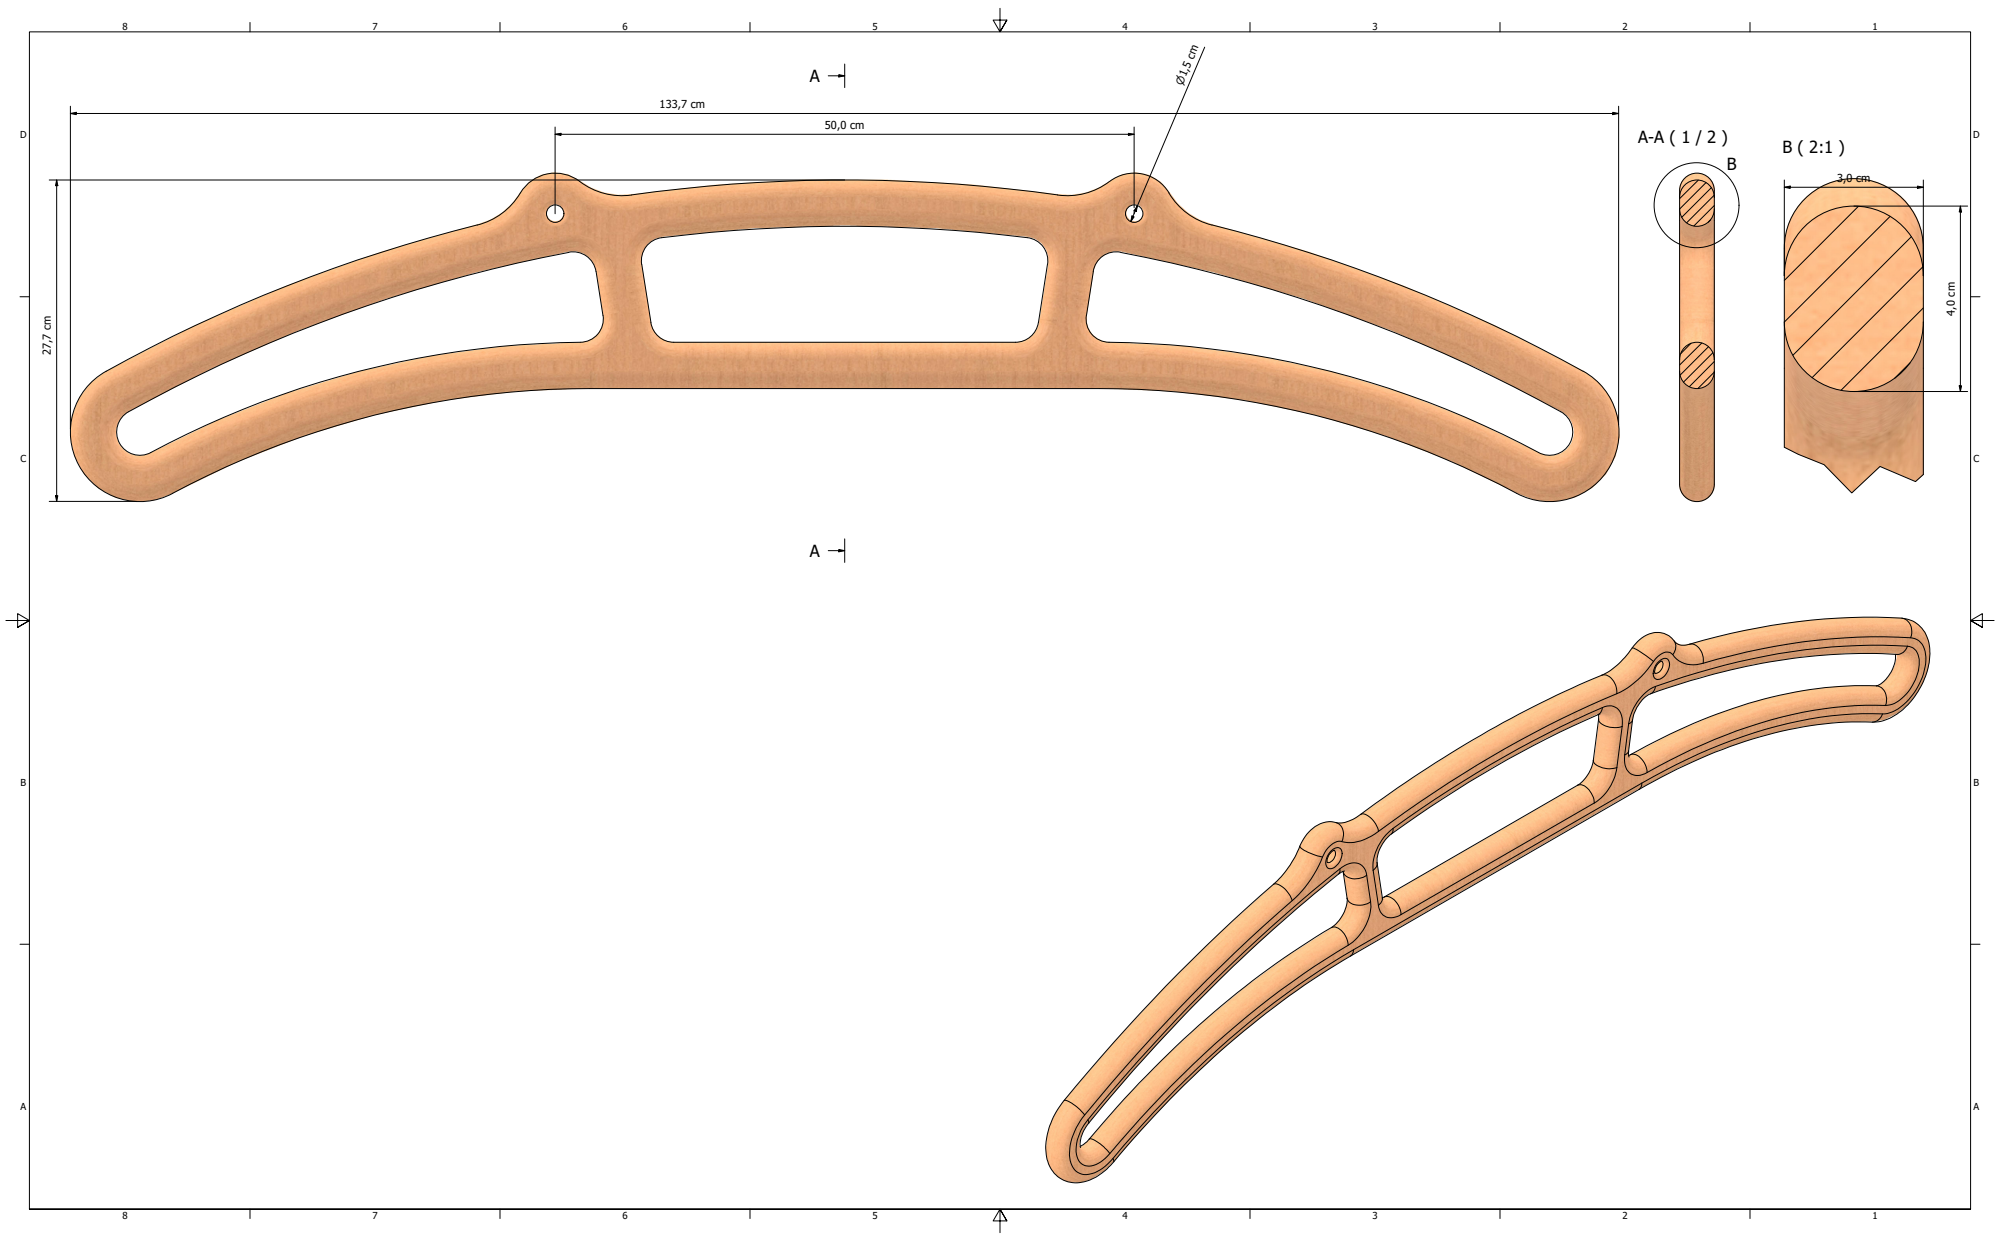
[picture p68: page 1]

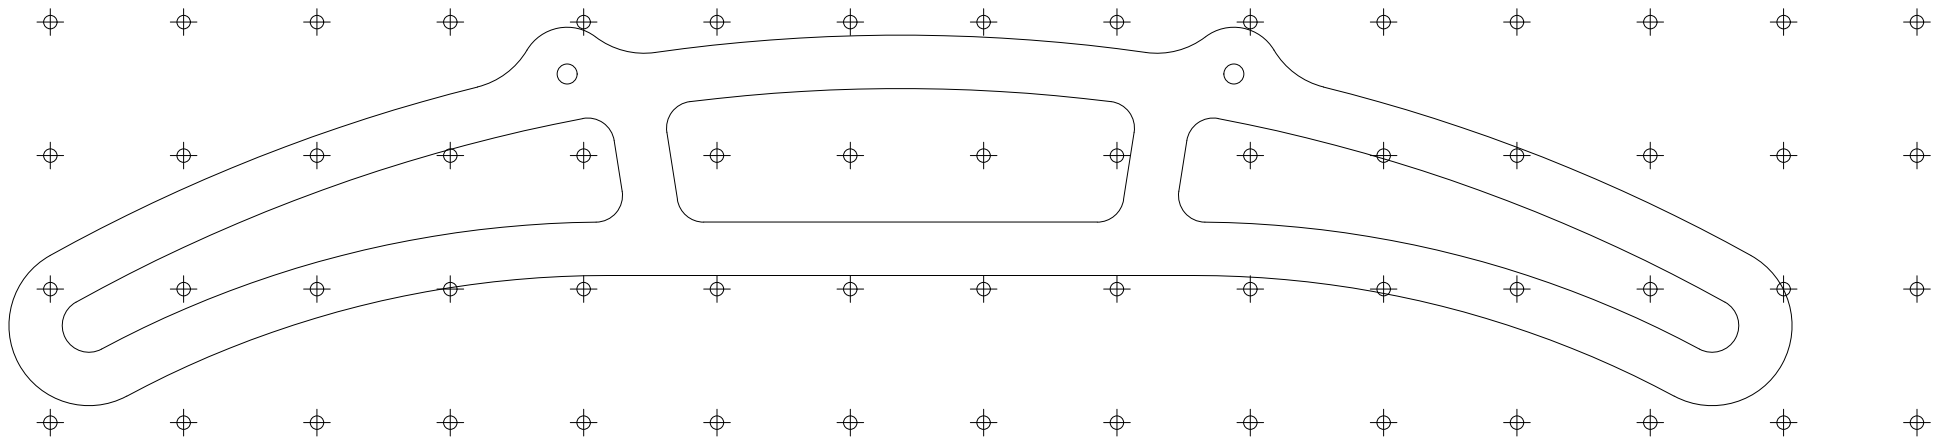
[picture p69: page 2]
